Opatusos/SNES_TST/Firmware/ip/snes_tst_cpu/synthesis/submodules/snes_tst_cpu_nios2_gen2_0_cpu.v

//Legal Notice: (C)2021 Altera Corporation. All rights reserved.  Your
//use of Altera Corporation's design tools, logic functions and other
//software and tools, and its AMPP partner logic functions, and any
//output files any of the foregoing (including device programming or
//simulation files), and any associated documentation or information are
//expressly subject to the terms and conditions of the Altera Program
//License Subscription Agreement or other applicable license agreement,
//including, without limitation, that your use is for the sole purpose
//of programming logic devices manufactured by Altera and sold by Altera
//or its authorized distributors.  Please refer to the applicable
//agreement for further details.

// synthesis translate_off
`timescale 1ns / 1ps
// synthesis translate_on

// turn off superfluous verilog processor warnings 
// altera message_level Level1 
// altera message_off 10034 10035 10036 10037 10230 10240 10030 

module snes_tst_cpu_nios2_gen2_0_cpu_register_bank_a_module (
                                                              // inputs:
                                                               clock,
                                                               data,
                                                               rdaddress,
                                                               wraddress,
                                                               wren,

                                                              // outputs:
                                                               q
                                                            )
;

  parameter lpm_file = "UNUSED";


  output  [ 31: 0] q;
  input            clock;
  input   [ 31: 0] data;
  input   [  4: 0] rdaddress;
  input   [  4: 0] wraddress;
  input            wren;


wire    [ 31: 0] q;
wire    [ 31: 0] ram_data;
wire    [ 31: 0] ram_q;
  assign q = ram_q;
  assign ram_data = data;
  altsyncram the_altsyncram
    (
      .address_a (wraddress),
      .address_b (rdaddress),
      .clock0 (clock),
      .data_a (ram_data),
      .q_b (ram_q),
      .wren_a (wren)
    );

  defparam the_altsyncram.address_reg_b = "CLOCK0",
           the_altsyncram.init_file = lpm_file,
           the_altsyncram.maximum_depth = 0,
           the_altsyncram.numwords_a = 32,
           the_altsyncram.numwords_b = 32,
           the_altsyncram.operation_mode = "DUAL_PORT",
           the_altsyncram.outdata_reg_b = "UNREGISTERED",
           the_altsyncram.ram_block_type = "AUTO",
           the_altsyncram.rdcontrol_reg_b = "CLOCK0",
           the_altsyncram.read_during_write_mode_mixed_ports = "DONT_CARE",
           the_altsyncram.width_a = 32,
           the_altsyncram.width_b = 32,
           the_altsyncram.widthad_a = 5,
           the_altsyncram.widthad_b = 5;


endmodule


// synthesis translate_off
`timescale 1ns / 1ps
// synthesis translate_on

// turn off superfluous verilog processor warnings 
// altera message_level Level1 
// altera message_off 10034 10035 10036 10037 10230 10240 10030 

module snes_tst_cpu_nios2_gen2_0_cpu_register_bank_b_module (
                                                              // inputs:
                                                               clock,
                                                               data,
                                                               rdaddress,
                                                               wraddress,
                                                               wren,

                                                              // outputs:
                                                               q
                                                            )
;

  parameter lpm_file = "UNUSED";


  output  [ 31: 0] q;
  input            clock;
  input   [ 31: 0] data;
  input   [  4: 0] rdaddress;
  input   [  4: 0] wraddress;
  input            wren;


wire    [ 31: 0] q;
wire    [ 31: 0] ram_data;
wire    [ 31: 0] ram_q;
  assign q = ram_q;
  assign ram_data = data;
  altsyncram the_altsyncram
    (
      .address_a (wraddress),
      .address_b (rdaddress),
      .clock0 (clock),
      .data_a (ram_data),
      .q_b (ram_q),
      .wren_a (wren)
    );

  defparam the_altsyncram.address_reg_b = "CLOCK0",
           the_altsyncram.init_file = lpm_file,
           the_altsyncram.maximum_depth = 0,
           the_altsyncram.numwords_a = 32,
           the_altsyncram.numwords_b = 32,
           the_altsyncram.operation_mode = "DUAL_PORT",
           the_altsyncram.outdata_reg_b = "UNREGISTERED",
           the_altsyncram.ram_block_type = "AUTO",
           the_altsyncram.rdcontrol_reg_b = "CLOCK0",
           the_altsyncram.read_during_write_mode_mixed_ports = "DONT_CARE",
           the_altsyncram.width_a = 32,
           the_altsyncram.width_b = 32,
           the_altsyncram.widthad_a = 5,
           the_altsyncram.widthad_b = 5;


endmodule


// synthesis translate_off
`timescale 1ns / 1ps
// synthesis translate_on

// turn off superfluous verilog processor warnings 
// altera message_level Level1 
// altera message_off 10034 10035 10036 10037 10230 10240 10030 

module snes_tst_cpu_nios2_gen2_0_cpu_nios2_oci_debug (
                                                       // inputs:
                                                        clk,
                                                        dbrk_break,
                                                        debugreq,
                                                        hbreak_enabled,
                                                        jdo,
                                                        jrst_n,
                                                        ocireg_ers,
                                                        ocireg_mrs,
                                                        reset,
                                                        st_ready_test_idle,
                                                        take_action_ocimem_a,
                                                        take_action_ocireg,
                                                        xbrk_break,

                                                       // outputs:
                                                        debugack,
                                                        monitor_error,
                                                        monitor_go,
                                                        monitor_ready,
                                                        oci_hbreak_req,
                                                        resetlatch,
                                                        resetrequest
                                                     )
;

  output           debugack;
  output           monitor_error;
  output           monitor_go;
  output           monitor_ready;
  output           oci_hbreak_req;
  output           resetlatch;
  output           resetrequest;
  input            clk;
  input            dbrk_break;
  input            debugreq;
  input            hbreak_enabled;
  input   [ 37: 0] jdo;
  input            jrst_n;
  input            ocireg_ers;
  input            ocireg_mrs;
  input            reset;
  input            st_ready_test_idle;
  input            take_action_ocimem_a;
  input            take_action_ocireg;
  input            xbrk_break;


reg              break_on_reset /* synthesis ALTERA_ATTRIBUTE = "SUPPRESS_DA_RULE_INTERNAL=\"D101,R101\""  */;
wire             debugack;
reg              jtag_break /* synthesis ALTERA_ATTRIBUTE = "SUPPRESS_DA_RULE_INTERNAL=\"D101,R101\""  */;
reg              monitor_error /* synthesis ALTERA_ATTRIBUTE = "SUPPRESS_DA_RULE_INTERNAL=D101"  */;
reg              monitor_go /* synthesis ALTERA_ATTRIBUTE = "SUPPRESS_DA_RULE_INTERNAL=D101"  */;
reg              monitor_ready /* synthesis ALTERA_ATTRIBUTE = "SUPPRESS_DA_RULE_INTERNAL=D101"  */;
wire             oci_hbreak_req;
wire             reset_sync;
reg              resetlatch /* synthesis ALTERA_ATTRIBUTE = "SUPPRESS_DA_RULE_INTERNAL=\"D101,R101\""  */;
reg              resetrequest /* synthesis ALTERA_ATTRIBUTE = "SUPPRESS_DA_RULE_INTERNAL=\"D101,R101\""  */;
wire             unxcomplemented_resetxx0;
  assign unxcomplemented_resetxx0 = jrst_n;
  altera_std_synchronizer the_altera_std_synchronizer
    (
      .clk (clk),
      .din (reset),
      .dout (reset_sync),
      .reset_n (unxcomplemented_resetxx0)
    );

  defparam the_altera_std_synchronizer.depth = 2;

  always @(posedge clk or negedge jrst_n)
    begin
      if (jrst_n == 0)
        begin
          resetrequest <= 1'b0;
          break_on_reset <= 1'b0;
          jtag_break <= 1'b0;
        end
      else if (take_action_ocimem_a)
        begin
          resetrequest <= jdo[22];
          jtag_break <= jdo[21]     ? 1 
                    : jdo[20]  ? 0 
                    : jtag_break;

          break_on_reset <= jdo[19]     ? 1
                    : jdo[18]  ? 0
                    :  break_on_reset;

          resetlatch <= jdo[24] ? 0 : resetlatch;
        end
      else if (reset_sync)
        begin
          jtag_break <= break_on_reset;
          resetlatch <= 1;
        end
      else if (debugreq & ~debugack & break_on_reset)
          jtag_break <= 1'b1;
    end


  always @(posedge clk or negedge jrst_n)
    begin
      if (jrst_n == 0)
        begin
          monitor_ready <= 1'b0;
          monitor_error <= 1'b0;
          monitor_go <= 1'b0;
        end
      else 
        begin
          if (take_action_ocimem_a && jdo[25])
              monitor_ready <= 1'b0;
          else if (take_action_ocireg && ocireg_mrs)
              monitor_ready <= 1'b1;
          if (take_action_ocimem_a && jdo[25])
              monitor_error <= 1'b0;
          else if (take_action_ocireg && ocireg_ers)
              monitor_error <= 1'b1;
          if (take_action_ocimem_a && jdo[23])
              monitor_go <= 1'b1;
          else if (st_ready_test_idle)
              monitor_go <= 1'b0;
        end
    end


  assign oci_hbreak_req = jtag_break | dbrk_break | xbrk_break | debugreq;
  assign debugack = ~hbreak_enabled;

endmodule


// synthesis translate_off
`timescale 1ns / 1ps
// synthesis translate_on

// turn off superfluous verilog processor warnings 
// altera message_level Level1 
// altera message_off 10034 10035 10036 10037 10230 10240 10030 

module snes_tst_cpu_nios2_gen2_0_cpu_nios2_oci_break (
                                                       // inputs:
                                                        clk,
                                                        dbrk_break,
                                                        dbrk_goto0,
                                                        dbrk_goto1,
                                                        jdo,
                                                        jrst_n,
                                                        take_action_break_a,
                                                        take_action_break_b,
                                                        take_action_break_c,
                                                        take_no_action_break_a,
                                                        take_no_action_break_b,
                                                        take_no_action_break_c,
                                                        xbrk_goto0,
                                                        xbrk_goto1,

                                                       // outputs:
                                                        break_readreg,
                                                        dbrk_hit0_latch,
                                                        dbrk_hit1_latch,
                                                        dbrk_hit2_latch,
                                                        dbrk_hit3_latch,
                                                        trigbrktype,
                                                        trigger_state_0,
                                                        trigger_state_1,
                                                        xbrk_ctrl0,
                                                        xbrk_ctrl1,
                                                        xbrk_ctrl2,
                                                        xbrk_ctrl3
                                                     )
;

  output  [ 31: 0] break_readreg;
  output           dbrk_hit0_latch;
  output           dbrk_hit1_latch;
  output           dbrk_hit2_latch;
  output           dbrk_hit3_latch;
  output           trigbrktype;
  output           trigger_state_0;
  output           trigger_state_1;
  output  [  7: 0] xbrk_ctrl0;
  output  [  7: 0] xbrk_ctrl1;
  output  [  7: 0] xbrk_ctrl2;
  output  [  7: 0] xbrk_ctrl3;
  input            clk;
  input            dbrk_break;
  input            dbrk_goto0;
  input            dbrk_goto1;
  input   [ 37: 0] jdo;
  input            jrst_n;
  input            take_action_break_a;
  input            take_action_break_b;
  input            take_action_break_c;
  input            take_no_action_break_a;
  input            take_no_action_break_b;
  input            take_no_action_break_c;
  input            xbrk_goto0;
  input            xbrk_goto1;


wire    [  3: 0] break_a_wpr;
wire    [  1: 0] break_a_wpr_high_bits;
wire    [  1: 0] break_a_wpr_low_bits;
wire    [  1: 0] break_b_rr;
wire    [  1: 0] break_c_rr;
reg     [ 31: 0] break_readreg /* synthesis ALTERA_ATTRIBUTE = "SUPPRESS_DA_RULE_INTERNAL=\"D101,R101\""  */;
wire             dbrk0_high_value;
wire             dbrk0_low_value;
wire             dbrk1_high_value;
wire             dbrk1_low_value;
wire             dbrk2_high_value;
wire             dbrk2_low_value;
wire             dbrk3_high_value;
wire             dbrk3_low_value;
wire             dbrk_hit0_latch;
wire             dbrk_hit1_latch;
wire             dbrk_hit2_latch;
wire             dbrk_hit3_latch;
wire             take_action_any_break;
reg              trigbrktype /* synthesis ALTERA_ATTRIBUTE = "SUPPRESS_DA_RULE_INTERNAL=\"D101,R101\""  */;
reg              trigger_state;
wire             trigger_state_0;
wire             trigger_state_1;
wire    [ 31: 0] xbrk0_value;
wire    [ 31: 0] xbrk1_value;
wire    [ 31: 0] xbrk2_value;
wire    [ 31: 0] xbrk3_value;
reg     [  7: 0] xbrk_ctrl0 /* synthesis ALTERA_ATTRIBUTE = "SUPPRESS_DA_RULE_INTERNAL=\"D101,R101\""  */;
reg     [  7: 0] xbrk_ctrl1 /* synthesis ALTERA_ATTRIBUTE = "SUPPRESS_DA_RULE_INTERNAL=\"D101,R101\""  */;
reg     [  7: 0] xbrk_ctrl2 /* synthesis ALTERA_ATTRIBUTE = "SUPPRESS_DA_RULE_INTERNAL=\"D101,R101\""  */;
reg     [  7: 0] xbrk_ctrl3 /* synthesis ALTERA_ATTRIBUTE = "SUPPRESS_DA_RULE_INTERNAL=\"D101,R101\""  */;
  assign break_a_wpr = jdo[35 : 32];
  assign break_a_wpr_high_bits = break_a_wpr[3 : 2];
  assign break_a_wpr_low_bits = break_a_wpr[1 : 0];
  assign break_b_rr = jdo[33 : 32];
  assign break_c_rr = jdo[33 : 32];
  assign take_action_any_break = take_action_break_a | take_action_break_b | take_action_break_c;
  always @(posedge clk or negedge jrst_n)
    begin
      if (jrst_n == 0)
        begin
          xbrk_ctrl0 <= 0;
          xbrk_ctrl1 <= 0;
          xbrk_ctrl2 <= 0;
          xbrk_ctrl3 <= 0;
          trigbrktype <= 0;
        end
      else 
        begin
          if (take_action_any_break)
              trigbrktype <= 0;
          else if (dbrk_break)
              trigbrktype <= 1;
          if (take_action_break_b)
            begin
              if ((break_b_rr == 2'b00) && (0 >= 1))
                begin
                  xbrk_ctrl0[0] <= jdo[27];
                  xbrk_ctrl0[1] <= jdo[28];
                  xbrk_ctrl0[2] <= jdo[29];
                  xbrk_ctrl0[3] <= jdo[30];
                  xbrk_ctrl0[4] <= jdo[21];
                  xbrk_ctrl0[5] <= jdo[20];
                  xbrk_ctrl0[6] <= jdo[19];
                  xbrk_ctrl0[7] <= jdo[18];
                end
              if ((break_b_rr == 2'b01) && (0 >= 2))
                begin
                  xbrk_ctrl1[0] <= jdo[27];
                  xbrk_ctrl1[1] <= jdo[28];
                  xbrk_ctrl1[2] <= jdo[29];
                  xbrk_ctrl1[3] <= jdo[30];
                  xbrk_ctrl1[4] <= jdo[21];
                  xbrk_ctrl1[5] <= jdo[20];
                  xbrk_ctrl1[6] <= jdo[19];
                  xbrk_ctrl1[7] <= jdo[18];
                end
              if ((break_b_rr == 2'b10) && (0 >= 3))
                begin
                  xbrk_ctrl2[0] <= jdo[27];
                  xbrk_ctrl2[1] <= jdo[28];
                  xbrk_ctrl2[2] <= jdo[29];
                  xbrk_ctrl2[3] <= jdo[30];
                  xbrk_ctrl2[4] <= jdo[21];
                  xbrk_ctrl2[5] <= jdo[20];
                  xbrk_ctrl2[6] <= jdo[19];
                  xbrk_ctrl2[7] <= jdo[18];
                end
              if ((break_b_rr == 2'b11) && (0 >= 4))
                begin
                  xbrk_ctrl3[0] <= jdo[27];
                  xbrk_ctrl3[1] <= jdo[28];
                  xbrk_ctrl3[2] <= jdo[29];
                  xbrk_ctrl3[3] <= jdo[30];
                  xbrk_ctrl3[4] <= jdo[21];
                  xbrk_ctrl3[5] <= jdo[20];
                  xbrk_ctrl3[6] <= jdo[19];
                  xbrk_ctrl3[7] <= jdo[18];
                end
            end
        end
    end


  assign dbrk_hit0_latch = 1'b0;
  assign dbrk0_low_value = 0;
  assign dbrk0_high_value = 0;
  assign dbrk_hit1_latch = 1'b0;
  assign dbrk1_low_value = 0;
  assign dbrk1_high_value = 0;
  assign dbrk_hit2_latch = 1'b0;
  assign dbrk2_low_value = 0;
  assign dbrk2_high_value = 0;
  assign dbrk_hit3_latch = 1'b0;
  assign dbrk3_low_value = 0;
  assign dbrk3_high_value = 0;
  assign xbrk0_value = 32'b0;
  assign xbrk1_value = 32'b0;
  assign xbrk2_value = 32'b0;
  assign xbrk3_value = 32'b0;
  always @(posedge clk or negedge jrst_n)
    begin
      if (jrst_n == 0)
          break_readreg <= 32'b0;
      else if (take_action_any_break)
          break_readreg <= jdo[31 : 0];
      else if (take_no_action_break_a)
          case (break_a_wpr_high_bits)
          
              2'd0: begin
                  case (break_a_wpr_low_bits) // synthesis full_case
                  
                      2'd0: begin
                          break_readreg <= xbrk0_value;
                      end // 2'd0 
                  
                      2'd1: begin
                          break_readreg <= xbrk1_value;
                      end // 2'd1 
                  
                      2'd2: begin
                          break_readreg <= xbrk2_value;
                      end // 2'd2 
                  
                      2'd3: begin
                          break_readreg <= xbrk3_value;
                      end // 2'd3 
                  
                  endcase // break_a_wpr_low_bits
              end // 2'd0 
          
              2'd1: begin
                  break_readreg <= 32'b0;
              end // 2'd1 
          
              2'd2: begin
                  case (break_a_wpr_low_bits) // synthesis full_case
                  
                      2'd0: begin
                          break_readreg <= dbrk0_low_value;
                      end // 2'd0 
                  
                      2'd1: begin
                          break_readreg <= dbrk1_low_value;
                      end // 2'd1 
                  
                      2'd2: begin
                          break_readreg <= dbrk2_low_value;
                      end // 2'd2 
                  
                      2'd3: begin
                          break_readreg <= dbrk3_low_value;
                      end // 2'd3 
                  
                  endcase // break_a_wpr_low_bits
              end // 2'd2 
          
              2'd3: begin
                  case (break_a_wpr_low_bits) // synthesis full_case
                  
                      2'd0: begin
                          break_readreg <= dbrk0_high_value;
                      end // 2'd0 
                  
                      2'd1: begin
                          break_readreg <= dbrk1_high_value;
                      end // 2'd1 
                  
                      2'd2: begin
                          break_readreg <= dbrk2_high_value;
                      end // 2'd2 
                  
                      2'd3: begin
                          break_readreg <= dbrk3_high_value;
                      end // 2'd3 
                  
                  endcase // break_a_wpr_low_bits
              end // 2'd3 
          
          endcase // break_a_wpr_high_bits
      else if (take_no_action_break_b)
          break_readreg <= jdo[31 : 0];
      else if (take_no_action_break_c)
          break_readreg <= jdo[31 : 0];
    end


  always @(posedge clk or negedge jrst_n)
    begin
      if (jrst_n == 0)
          trigger_state <= 0;
      else if (trigger_state_1 & (xbrk_goto0 | dbrk_goto0))
          trigger_state <= 0;
      else if (trigger_state_0 & (xbrk_goto1 | dbrk_goto1))
          trigger_state <= -1;
    end


  assign trigger_state_0 = ~trigger_state;
  assign trigger_state_1 = trigger_state;

endmodule


// synthesis translate_off
`timescale 1ns / 1ps
// synthesis translate_on

// turn off superfluous verilog processor warnings 
// altera message_level Level1 
// altera message_off 10034 10035 10036 10037 10230 10240 10030 

module snes_tst_cpu_nios2_gen2_0_cpu_nios2_oci_xbrk (
                                                      // inputs:
                                                       D_valid,
                                                       E_valid,
                                                       F_pc,
                                                       clk,
                                                       reset_n,
                                                       trigger_state_0,
                                                       trigger_state_1,
                                                       xbrk_ctrl0,
                                                       xbrk_ctrl1,
                                                       xbrk_ctrl2,
                                                       xbrk_ctrl3,

                                                      // outputs:
                                                       xbrk_break,
                                                       xbrk_goto0,
                                                       xbrk_goto1,
                                                       xbrk_traceoff,
                                                       xbrk_traceon,
                                                       xbrk_trigout
                                                    )
;

  output           xbrk_break;
  output           xbrk_goto0;
  output           xbrk_goto1;
  output           xbrk_traceoff;
  output           xbrk_traceon;
  output           xbrk_trigout;
  input            D_valid;
  input            E_valid;
  input   [ 17: 0] F_pc;
  input            clk;
  input            reset_n;
  input            trigger_state_0;
  input            trigger_state_1;
  input   [  7: 0] xbrk_ctrl0;
  input   [  7: 0] xbrk_ctrl1;
  input   [  7: 0] xbrk_ctrl2;
  input   [  7: 0] xbrk_ctrl3;


wire             D_cpu_addr_en;
wire             E_cpu_addr_en;
reg              E_xbrk_goto0;
reg              E_xbrk_goto1;
reg              E_xbrk_traceoff;
reg              E_xbrk_traceon;
reg              E_xbrk_trigout;
wire    [ 19: 0] cpu_i_address;
wire             xbrk0_armed;
wire             xbrk0_break_hit;
wire             xbrk0_goto0_hit;
wire             xbrk0_goto1_hit;
wire             xbrk0_toff_hit;
wire             xbrk0_ton_hit;
wire             xbrk0_tout_hit;
wire             xbrk1_armed;
wire             xbrk1_break_hit;
wire             xbrk1_goto0_hit;
wire             xbrk1_goto1_hit;
wire             xbrk1_toff_hit;
wire             xbrk1_ton_hit;
wire             xbrk1_tout_hit;
wire             xbrk2_armed;
wire             xbrk2_break_hit;
wire             xbrk2_goto0_hit;
wire             xbrk2_goto1_hit;
wire             xbrk2_toff_hit;
wire             xbrk2_ton_hit;
wire             xbrk2_tout_hit;
wire             xbrk3_armed;
wire             xbrk3_break_hit;
wire             xbrk3_goto0_hit;
wire             xbrk3_goto1_hit;
wire             xbrk3_toff_hit;
wire             xbrk3_ton_hit;
wire             xbrk3_tout_hit;
reg              xbrk_break;
wire             xbrk_break_hit;
wire             xbrk_goto0;
wire             xbrk_goto0_hit;
wire             xbrk_goto1;
wire             xbrk_goto1_hit;
wire             xbrk_toff_hit;
wire             xbrk_ton_hit;
wire             xbrk_tout_hit;
wire             xbrk_traceoff;
wire             xbrk_traceon;
wire             xbrk_trigout;
  assign cpu_i_address = {F_pc, 2'b00};
  assign D_cpu_addr_en = D_valid;
  assign E_cpu_addr_en = E_valid;
  assign xbrk0_break_hit = 0;
  assign xbrk0_ton_hit = 0;
  assign xbrk0_toff_hit = 0;
  assign xbrk0_tout_hit = 0;
  assign xbrk0_goto0_hit = 0;
  assign xbrk0_goto1_hit = 0;
  assign xbrk1_break_hit = 0;
  assign xbrk1_ton_hit = 0;
  assign xbrk1_toff_hit = 0;
  assign xbrk1_tout_hit = 0;
  assign xbrk1_goto0_hit = 0;
  assign xbrk1_goto1_hit = 0;
  assign xbrk2_break_hit = 0;
  assign xbrk2_ton_hit = 0;
  assign xbrk2_toff_hit = 0;
  assign xbrk2_tout_hit = 0;
  assign xbrk2_goto0_hit = 0;
  assign xbrk2_goto1_hit = 0;
  assign xbrk3_break_hit = 0;
  assign xbrk3_ton_hit = 0;
  assign xbrk3_toff_hit = 0;
  assign xbrk3_tout_hit = 0;
  assign xbrk3_goto0_hit = 0;
  assign xbrk3_goto1_hit = 0;
  assign xbrk_break_hit = (xbrk0_break_hit) | (xbrk1_break_hit) | (xbrk2_break_hit) | (xbrk3_break_hit);
  assign xbrk_ton_hit = (xbrk0_ton_hit) | (xbrk1_ton_hit) | (xbrk2_ton_hit) | (xbrk3_ton_hit);
  assign xbrk_toff_hit = (xbrk0_toff_hit) | (xbrk1_toff_hit) | (xbrk2_toff_hit) | (xbrk3_toff_hit);
  assign xbrk_tout_hit = (xbrk0_tout_hit) | (xbrk1_tout_hit) | (xbrk2_tout_hit) | (xbrk3_tout_hit);
  assign xbrk_goto0_hit = (xbrk0_goto0_hit) | (xbrk1_goto0_hit) | (xbrk2_goto0_hit) | (xbrk3_goto0_hit);
  assign xbrk_goto1_hit = (xbrk0_goto1_hit) | (xbrk1_goto1_hit) | (xbrk2_goto1_hit) | (xbrk3_goto1_hit);
  always @(posedge clk or negedge reset_n)
    begin
      if (reset_n == 0)
          xbrk_break <= 0;
      else if (E_cpu_addr_en)
          xbrk_break <= xbrk_break_hit;
    end


  always @(posedge clk or negedge reset_n)
    begin
      if (reset_n == 0)
          E_xbrk_traceon <= 0;
      else if (E_cpu_addr_en)
          E_xbrk_traceon <= xbrk_ton_hit;
    end


  always @(posedge clk or negedge reset_n)
    begin
      if (reset_n == 0)
          E_xbrk_traceoff <= 0;
      else if (E_cpu_addr_en)
          E_xbrk_traceoff <= xbrk_toff_hit;
    end


  always @(posedge clk or negedge reset_n)
    begin
      if (reset_n == 0)
          E_xbrk_trigout <= 0;
      else if (E_cpu_addr_en)
          E_xbrk_trigout <= xbrk_tout_hit;
    end


  always @(posedge clk or negedge reset_n)
    begin
      if (reset_n == 0)
          E_xbrk_goto0 <= 0;
      else if (E_cpu_addr_en)
          E_xbrk_goto0 <= xbrk_goto0_hit;
    end


  always @(posedge clk or negedge reset_n)
    begin
      if (reset_n == 0)
          E_xbrk_goto1 <= 0;
      else if (E_cpu_addr_en)
          E_xbrk_goto1 <= xbrk_goto1_hit;
    end


  assign xbrk_traceon = 1'b0;
  assign xbrk_traceoff = 1'b0;
  assign xbrk_trigout = 1'b0;
  assign xbrk_goto0 = 1'b0;
  assign xbrk_goto1 = 1'b0;
  assign xbrk0_armed = (xbrk_ctrl0[4] & trigger_state_0) ||
    (xbrk_ctrl0[5] & trigger_state_1);

  assign xbrk1_armed = (xbrk_ctrl1[4] & trigger_state_0) ||
    (xbrk_ctrl1[5] & trigger_state_1);

  assign xbrk2_armed = (xbrk_ctrl2[4] & trigger_state_0) ||
    (xbrk_ctrl2[5] & trigger_state_1);

  assign xbrk3_armed = (xbrk_ctrl3[4] & trigger_state_0) ||
    (xbrk_ctrl3[5] & trigger_state_1);


endmodule


// synthesis translate_off
`timescale 1ns / 1ps
// synthesis translate_on

// turn off superfluous verilog processor warnings 
// altera message_level Level1 
// altera message_off 10034 10035 10036 10037 10230 10240 10030 

module snes_tst_cpu_nios2_gen2_0_cpu_nios2_oci_dbrk (
                                                      // inputs:
                                                       E_st_data,
                                                       av_ld_data_aligned_filtered,
                                                       clk,
                                                       d_address,
                                                       d_read,
                                                       d_waitrequest,
                                                       d_write,
                                                       debugack,
                                                       reset_n,

                                                      // outputs:
                                                       cpu_d_address,
                                                       cpu_d_read,
                                                       cpu_d_readdata,
                                                       cpu_d_wait,
                                                       cpu_d_write,
                                                       cpu_d_writedata,
                                                       dbrk_break,
                                                       dbrk_goto0,
                                                       dbrk_goto1,
                                                       dbrk_traceme,
                                                       dbrk_traceoff,
                                                       dbrk_traceon,
                                                       dbrk_trigout
                                                    )
;

  output  [ 19: 0] cpu_d_address;
  output           cpu_d_read;
  output  [ 31: 0] cpu_d_readdata;
  output           cpu_d_wait;
  output           cpu_d_write;
  output  [ 31: 0] cpu_d_writedata;
  output           dbrk_break;
  output           dbrk_goto0;
  output           dbrk_goto1;
  output           dbrk_traceme;
  output           dbrk_traceoff;
  output           dbrk_traceon;
  output           dbrk_trigout;
  input   [ 31: 0] E_st_data;
  input   [ 31: 0] av_ld_data_aligned_filtered;
  input            clk;
  input   [ 19: 0] d_address;
  input            d_read;
  input            d_waitrequest;
  input            d_write;
  input            debugack;
  input            reset_n;


wire    [ 19: 0] cpu_d_address;
wire             cpu_d_read;
wire    [ 31: 0] cpu_d_readdata;
wire             cpu_d_wait;
wire             cpu_d_write;
wire    [ 31: 0] cpu_d_writedata;
wire             dbrk0_armed;
wire             dbrk0_break_pulse;
wire             dbrk0_goto0;
wire             dbrk0_goto1;
wire             dbrk0_traceme;
wire             dbrk0_traceoff;
wire             dbrk0_traceon;
wire             dbrk0_trigout;
wire             dbrk1_armed;
wire             dbrk1_break_pulse;
wire             dbrk1_goto0;
wire             dbrk1_goto1;
wire             dbrk1_traceme;
wire             dbrk1_traceoff;
wire             dbrk1_traceon;
wire             dbrk1_trigout;
wire             dbrk2_armed;
wire             dbrk2_break_pulse;
wire             dbrk2_goto0;
wire             dbrk2_goto1;
wire             dbrk2_traceme;
wire             dbrk2_traceoff;
wire             dbrk2_traceon;
wire             dbrk2_trigout;
wire             dbrk3_armed;
wire             dbrk3_break_pulse;
wire             dbrk3_goto0;
wire             dbrk3_goto1;
wire             dbrk3_traceme;
wire             dbrk3_traceoff;
wire             dbrk3_traceon;
wire             dbrk3_trigout;
reg              dbrk_break;
reg              dbrk_break_pulse;
wire    [ 31: 0] dbrk_data;
reg              dbrk_goto0;
reg              dbrk_goto1;
reg              dbrk_traceme;
reg              dbrk_traceoff;
reg              dbrk_traceon;
reg              dbrk_trigout;
  assign cpu_d_address = d_address;
  assign cpu_d_readdata = av_ld_data_aligned_filtered;
  assign cpu_d_read = d_read;
  assign cpu_d_writedata = E_st_data;
  assign cpu_d_write = d_write;
  assign cpu_d_wait = d_waitrequest;
  assign dbrk_data = cpu_d_write ? cpu_d_writedata : cpu_d_readdata;
  always @(posedge clk or negedge reset_n)
    begin
      if (reset_n == 0)
          dbrk_break <= 0;
      else 
        dbrk_break <= dbrk_break   ? ~debugack   
                : dbrk_break_pulse;

    end


  assign dbrk0_armed = 1'b0;
  assign dbrk0_trigout = 1'b0;
  assign dbrk0_break_pulse = 1'b0;
  assign dbrk0_traceoff = 1'b0;
  assign dbrk0_traceon = 1'b0;
  assign dbrk0_traceme = 1'b0;
  assign dbrk0_goto0 = 1'b0;
  assign dbrk0_goto1 = 1'b0;
  assign dbrk1_armed = 1'b0;
  assign dbrk1_trigout = 1'b0;
  assign dbrk1_break_pulse = 1'b0;
  assign dbrk1_traceoff = 1'b0;
  assign dbrk1_traceon = 1'b0;
  assign dbrk1_traceme = 1'b0;
  assign dbrk1_goto0 = 1'b0;
  assign dbrk1_goto1 = 1'b0;
  assign dbrk2_armed = 1'b0;
  assign dbrk2_trigout = 1'b0;
  assign dbrk2_break_pulse = 1'b0;
  assign dbrk2_traceoff = 1'b0;
  assign dbrk2_traceon = 1'b0;
  assign dbrk2_traceme = 1'b0;
  assign dbrk2_goto0 = 1'b0;
  assign dbrk2_goto1 = 1'b0;
  assign dbrk3_armed = 1'b0;
  assign dbrk3_trigout = 1'b0;
  assign dbrk3_break_pulse = 1'b0;
  assign dbrk3_traceoff = 1'b0;
  assign dbrk3_traceon = 1'b0;
  assign dbrk3_traceme = 1'b0;
  assign dbrk3_goto0 = 1'b0;
  assign dbrk3_goto1 = 1'b0;
  always @(posedge clk or negedge reset_n)
    begin
      if (reset_n == 0)
        begin
          dbrk_trigout <= 0;
          dbrk_break_pulse <= 0;
          dbrk_traceoff <= 0;
          dbrk_traceon <= 0;
          dbrk_traceme <= 0;
          dbrk_goto0 <= 0;
          dbrk_goto1 <= 0;
        end
      else 
        begin
          dbrk_trigout <= dbrk0_trigout | dbrk1_trigout | dbrk2_trigout | dbrk3_trigout;
          dbrk_break_pulse <= dbrk0_break_pulse | dbrk1_break_pulse | dbrk2_break_pulse | dbrk3_break_pulse;
          dbrk_traceoff <= dbrk0_traceoff | dbrk1_traceoff | dbrk2_traceoff | dbrk3_traceoff;
          dbrk_traceon <= dbrk0_traceon | dbrk1_traceon | dbrk2_traceon | dbrk3_traceon;
          dbrk_traceme <= dbrk0_traceme | dbrk1_traceme | dbrk2_traceme | dbrk3_traceme;
          dbrk_goto0 <= dbrk0_goto0 | dbrk1_goto0 | dbrk2_goto0 | dbrk3_goto0;
          dbrk_goto1 <= dbrk0_goto1 | dbrk1_goto1 | dbrk2_goto1 | dbrk3_goto1;
        end
    end



endmodule


// synthesis translate_off
`timescale 1ns / 1ps
// synthesis translate_on

// turn off superfluous verilog processor warnings 
// altera message_level Level1 
// altera message_off 10034 10035 10036 10037 10230 10240 10030 

module snes_tst_cpu_nios2_gen2_0_cpu_nios2_oci_itrace (
                                                        // inputs:
                                                         clk,
                                                         dbrk_traceoff,
                                                         dbrk_traceon,
                                                         jdo,
                                                         jrst_n,
                                                         take_action_tracectrl,
                                                         xbrk_traceoff,
                                                         xbrk_traceon,
                                                         xbrk_wrap_traceoff,

                                                        // outputs:
                                                         itm,
                                                         trc_ctrl,
                                                         trc_on
                                                      )
;

  output  [ 35: 0] itm;
  output  [ 15: 0] trc_ctrl;
  output           trc_on;
  input            clk;
  input            dbrk_traceoff;
  input            dbrk_traceon;
  input   [ 15: 0] jdo;
  input            jrst_n;
  input            take_action_tracectrl;
  input            xbrk_traceoff;
  input            xbrk_traceon;
  input            xbrk_wrap_traceoff;


wire             advanced_exc_occured;
wire             curr_pid;
wire    [  1: 0] dct_code;
wire             dct_is_taken;
wire    [ 31: 0] eic_addr;
wire    [ 31: 0] exc_addr;
wire             instr_retired;
wire             is_cond_dct;
wire             is_dct;
wire             is_exception_no_break;
wire             is_external_interrupt;
wire             is_fast_tlb_miss_exception;
wire             is_idct;
wire    [ 35: 0] itm;
wire             not_in_debug_mode;
wire             record_dct_outcome_in_sync;
wire             record_itrace;
wire    [ 31: 0] retired_pcb;
wire    [  1: 0] sync_code;
wire    [  6: 0] sync_interval;
wire    [  6: 0] sync_timer;
wire    [  6: 0] sync_timer_next;
wire             sync_timer_reached_zero;
wire    [ 15: 0] trc_ctrl;
reg     [ 10: 0] trc_ctrl_reg /* synthesis ALTERA_ATTRIBUTE = "SUPPRESS_DA_RULE_INTERNAL=\"D101,D103,R101\""  */;
wire             trc_on;
  assign is_cond_dct = 1'b0;
  assign is_dct = 1'b0;
  assign dct_is_taken = 1'b0;
  assign is_idct = 1'b0;
  assign retired_pcb = 32'b0;
  assign not_in_debug_mode = 1'b0;
  assign instr_retired = 1'b0;
  assign advanced_exc_occured = 1'b0;
  assign is_exception_no_break = 1'b0;
  assign is_external_interrupt = 1'b0;
  assign is_fast_tlb_miss_exception = 1'b0;
  assign curr_pid = 1'b0;
  assign exc_addr = 32'b0;
  assign eic_addr = 32'b0;
  assign sync_code = trc_ctrl[3 : 2];
  assign sync_interval = { sync_code[1] & sync_code[0], 1'b0, sync_code[1] & ~sync_code[0], 1'b0, ~sync_code[1] & sync_code[0], 2'b00 };
  assign sync_timer_reached_zero = sync_timer == 0;
  assign record_dct_outcome_in_sync = dct_is_taken & sync_timer_reached_zero;
  assign sync_timer_next = sync_timer_reached_zero ? sync_timer : (sync_timer - 1);
  assign record_itrace = trc_on & trc_ctrl[4];
  assign dct_code = {is_cond_dct, dct_is_taken};
  assign itm = 36'd0;
  assign sync_timer = 7'd1;
  always @(posedge clk or negedge jrst_n)
    begin
      if (jrst_n == 0)
        begin
          trc_ctrl_reg[0] <= 1'b0;
          trc_ctrl_reg[1] <= 1'b0;
          trc_ctrl_reg[3 : 2] <= 2'b00;
          trc_ctrl_reg[4] <= 1'b0;
          trc_ctrl_reg[7 : 5] <= 3'b000;
          trc_ctrl_reg[8] <= 0;
          trc_ctrl_reg[9] <= 1'b0;
          trc_ctrl_reg[10] <= 1'b0;
        end
      else if (take_action_tracectrl)
        begin
          trc_ctrl_reg[0] <= jdo[5];
          trc_ctrl_reg[1] <= jdo[6];
          trc_ctrl_reg[3 : 2] <= jdo[8 : 7];
          trc_ctrl_reg[4] <= jdo[9];
          trc_ctrl_reg[9] <= jdo[14];
          trc_ctrl_reg[10] <= jdo[2];
          trc_ctrl_reg[7 : 5] <= 3'b000;
          trc_ctrl_reg[8] <= 1'b0;
        end
      else if (xbrk_wrap_traceoff)
        begin
          trc_ctrl_reg[1] <= 0;
          trc_ctrl_reg[0] <= 0;
        end
      else if (dbrk_traceoff | xbrk_traceoff)
          trc_ctrl_reg[1] <= 0;
      else if (trc_ctrl_reg[0] & 
                                  (dbrk_traceon | xbrk_traceon))
          trc_ctrl_reg[1] <= 1;
    end


  assign trc_ctrl = 0;
  assign trc_on = trc_ctrl[1] & (trc_ctrl[9] | not_in_debug_mode);

endmodule


// synthesis translate_off
`timescale 1ns / 1ps
// synthesis translate_on

// turn off superfluous verilog processor warnings 
// altera message_level Level1 
// altera message_off 10034 10035 10036 10037 10230 10240 10030 

module snes_tst_cpu_nios2_gen2_0_cpu_nios2_oci_td_mode (
                                                         // inputs:
                                                          ctrl,

                                                         // outputs:
                                                          td_mode
                                                       )
;

  output  [  3: 0] td_mode;
  input   [  8: 0] ctrl;


wire    [  2: 0] ctrl_bits_for_mux;
reg     [  3: 0] td_mode;
  assign ctrl_bits_for_mux = ctrl[7 : 5];
  always @(ctrl_bits_for_mux)
    begin
      case (ctrl_bits_for_mux)
      
          3'b000: begin
              td_mode = 4'b0000;
          end // 3'b000 
      
          3'b001: begin
              td_mode = 4'b1000;
          end // 3'b001 
      
          3'b010: begin
              td_mode = 4'b0100;
          end // 3'b010 
      
          3'b011: begin
              td_mode = 4'b1100;
          end // 3'b011 
      
          3'b100: begin
              td_mode = 4'b0010;
          end // 3'b100 
      
          3'b101: begin
              td_mode = 4'b1010;
          end // 3'b101 
      
          3'b110: begin
              td_mode = 4'b0101;
          end // 3'b110 
      
          3'b111: begin
              td_mode = 4'b1111;
          end // 3'b111 
      
      endcase // ctrl_bits_for_mux
    end



endmodule


// synthesis translate_off
`timescale 1ns / 1ps
// synthesis translate_on

// turn off superfluous verilog processor warnings 
// altera message_level Level1 
// altera message_off 10034 10035 10036 10037 10230 10240 10030 

module snes_tst_cpu_nios2_gen2_0_cpu_nios2_oci_dtrace (
                                                        // inputs:
                                                         clk,
                                                         cpu_d_address,
                                                         cpu_d_read,
                                                         cpu_d_readdata,
                                                         cpu_d_wait,
                                                         cpu_d_write,
                                                         cpu_d_writedata,
                                                         jrst_n,
                                                         trc_ctrl,

                                                        // outputs:
                                                         atm,
                                                         dtm
                                                      )
;

  output  [ 35: 0] atm;
  output  [ 35: 0] dtm;
  input            clk;
  input   [ 19: 0] cpu_d_address;
  input            cpu_d_read;
  input   [ 31: 0] cpu_d_readdata;
  input            cpu_d_wait;
  input            cpu_d_write;
  input   [ 31: 0] cpu_d_writedata;
  input            jrst_n;
  input   [ 15: 0] trc_ctrl;


reg     [ 35: 0] atm /* synthesis ALTERA_ATTRIBUTE = "SUPPRESS_DA_RULE_INTERNAL=R101"  */;
wire    [ 31: 0] cpu_d_address_0_padded;
wire    [ 31: 0] cpu_d_readdata_0_padded;
wire    [ 31: 0] cpu_d_writedata_0_padded;
reg     [ 35: 0] dtm /* synthesis ALTERA_ATTRIBUTE = "SUPPRESS_DA_RULE_INTERNAL=R101"  */;
wire             dummy_tie_off;
wire             record_load_addr;
wire             record_load_data;
wire             record_store_addr;
wire             record_store_data;
wire    [  3: 0] td_mode_trc_ctrl;
  assign cpu_d_writedata_0_padded = cpu_d_writedata | 32'b0;
  assign cpu_d_readdata_0_padded = cpu_d_readdata | 32'b0;
  assign cpu_d_address_0_padded = cpu_d_address | 32'b0;
  //snes_tst_cpu_nios2_gen2_0_cpu_nios2_oci_trc_ctrl_td_mode, which is an e_instance
  snes_tst_cpu_nios2_gen2_0_cpu_nios2_oci_td_mode snes_tst_cpu_nios2_gen2_0_cpu_nios2_oci_trc_ctrl_td_mode
    (
      .ctrl    (trc_ctrl[8 : 0]),
      .td_mode (td_mode_trc_ctrl)
    );

  assign {record_load_addr, record_store_addr,
         record_load_data, record_store_data} = td_mode_trc_ctrl;
  always @(posedge clk or negedge jrst_n)
    begin
      if (jrst_n == 0)
        begin
          atm <= 0;
          dtm <= 0;
        end
      else 
        begin
          atm <= 0;
          dtm <= 0;
        end
    end


  assign dummy_tie_off = cpu_d_wait|cpu_d_read|cpu_d_write;

endmodule


// synthesis translate_off
`timescale 1ns / 1ps
// synthesis translate_on

// turn off superfluous verilog processor warnings 
// altera message_level Level1 
// altera message_off 10034 10035 10036 10037 10230 10240 10030 

module snes_tst_cpu_nios2_gen2_0_cpu_nios2_oci_compute_input_tm_cnt (
                                                                      // inputs:
                                                                       atm_valid,
                                                                       dtm_valid,
                                                                       itm_valid,

                                                                      // outputs:
                                                                       compute_input_tm_cnt
                                                                    )
;

  output  [  1: 0] compute_input_tm_cnt;
  input            atm_valid;
  input            dtm_valid;
  input            itm_valid;


reg     [  1: 0] compute_input_tm_cnt;
wire    [  2: 0] switch_for_mux;
  assign switch_for_mux = {itm_valid, atm_valid, dtm_valid};
  always @(switch_for_mux)
    begin
      case (switch_for_mux)
      
          3'b000: begin
              compute_input_tm_cnt = 0;
          end // 3'b000 
      
          3'b001: begin
              compute_input_tm_cnt = 1;
          end // 3'b001 
      
          3'b010: begin
              compute_input_tm_cnt = 1;
          end // 3'b010 
      
          3'b011: begin
              compute_input_tm_cnt = 2;
          end // 3'b011 
      
          3'b100: begin
              compute_input_tm_cnt = 1;
          end // 3'b100 
      
          3'b101: begin
              compute_input_tm_cnt = 2;
          end // 3'b101 
      
          3'b110: begin
              compute_input_tm_cnt = 2;
          end // 3'b110 
      
          3'b111: begin
              compute_input_tm_cnt = 3;
          end // 3'b111 
      
      endcase // switch_for_mux
    end



endmodule


// synthesis translate_off
`timescale 1ns / 1ps
// synthesis translate_on

// turn off superfluous verilog processor warnings 
// altera message_level Level1 
// altera message_off 10034 10035 10036 10037 10230 10240 10030 

module snes_tst_cpu_nios2_gen2_0_cpu_nios2_oci_fifo_wrptr_inc (
                                                                // inputs:
                                                                 ge2_free,
                                                                 ge3_free,
                                                                 input_tm_cnt,

                                                                // outputs:
                                                                 fifo_wrptr_inc
                                                              )
;

  output  [  3: 0] fifo_wrptr_inc;
  input            ge2_free;
  input            ge3_free;
  input   [  1: 0] input_tm_cnt;


reg     [  3: 0] fifo_wrptr_inc;
  always @(ge2_free or ge3_free or input_tm_cnt)
    begin
      if (ge3_free & (input_tm_cnt == 3))
          fifo_wrptr_inc = 3;
      else if (ge2_free & (input_tm_cnt >= 2))
          fifo_wrptr_inc = 2;
      else if (input_tm_cnt >= 1)
          fifo_wrptr_inc = 1;
      else 
        fifo_wrptr_inc = 0;
    end



endmodule


// synthesis translate_off
`timescale 1ns / 1ps
// synthesis translate_on

// turn off superfluous verilog processor warnings 
// altera message_level Level1 
// altera message_off 10034 10035 10036 10037 10230 10240 10030 

module snes_tst_cpu_nios2_gen2_0_cpu_nios2_oci_fifo_cnt_inc (
                                                              // inputs:
                                                               empty,
                                                               ge2_free,
                                                               ge3_free,
                                                               input_tm_cnt,

                                                              // outputs:
                                                               fifo_cnt_inc
                                                            )
;

  output  [  4: 0] fifo_cnt_inc;
  input            empty;
  input            ge2_free;
  input            ge3_free;
  input   [  1: 0] input_tm_cnt;


reg     [  4: 0] fifo_cnt_inc;
  always @(empty or ge2_free or ge3_free or input_tm_cnt)
    begin
      if (empty)
          fifo_cnt_inc = input_tm_cnt[1 : 0];
      else if (ge3_free & (input_tm_cnt == 3))
          fifo_cnt_inc = 2;
      else if (ge2_free & (input_tm_cnt >= 2))
          fifo_cnt_inc = 1;
      else if (input_tm_cnt >= 1)
          fifo_cnt_inc = 0;
      else 
        fifo_cnt_inc = {5{1'b1}};
    end



endmodule


// synthesis translate_off
`timescale 1ns / 1ps
// synthesis translate_on

// turn off superfluous verilog processor warnings 
// altera message_level Level1 
// altera message_off 10034 10035 10036 10037 10230 10240 10030 

module snes_tst_cpu_nios2_gen2_0_cpu_nios2_oci_fifo (
                                                      // inputs:
                                                       atm,
                                                       clk,
                                                       dbrk_traceme,
                                                       dbrk_traceoff,
                                                       dbrk_traceon,
                                                       dtm,
                                                       itm,
                                                       jrst_n,
                                                       reset_n,
                                                       trc_on,

                                                      // outputs:
                                                       tw
                                                    )
;

  output  [ 35: 0] tw;
  input   [ 35: 0] atm;
  input            clk;
  input            dbrk_traceme;
  input            dbrk_traceoff;
  input            dbrk_traceon;
  input   [ 35: 0] dtm;
  input   [ 35: 0] itm;
  input            jrst_n;
  input            reset_n;
  input            trc_on;


wire             atm_valid;
wire    [  1: 0] compute_input_tm_cnt;
wire             dtm_valid;
wire             empty;
reg     [ 35: 0] fifo_0;
wire             fifo_0_enable;
wire    [ 35: 0] fifo_0_mux;
reg     [ 35: 0] fifo_1;
reg     [ 35: 0] fifo_10;
wire             fifo_10_enable;
wire    [ 35: 0] fifo_10_mux;
reg     [ 35: 0] fifo_11;
wire             fifo_11_enable;
wire    [ 35: 0] fifo_11_mux;
reg     [ 35: 0] fifo_12;
wire             fifo_12_enable;
wire    [ 35: 0] fifo_12_mux;
reg     [ 35: 0] fifo_13;
wire             fifo_13_enable;
wire    [ 35: 0] fifo_13_mux;
reg     [ 35: 0] fifo_14;
wire             fifo_14_enable;
wire    [ 35: 0] fifo_14_mux;
reg     [ 35: 0] fifo_15;
wire             fifo_15_enable;
wire    [ 35: 0] fifo_15_mux;
wire             fifo_1_enable;
wire    [ 35: 0] fifo_1_mux;
reg     [ 35: 0] fifo_2;
wire             fifo_2_enable;
wire    [ 35: 0] fifo_2_mux;
reg     [ 35: 0] fifo_3;
wire             fifo_3_enable;
wire    [ 35: 0] fifo_3_mux;
reg     [ 35: 0] fifo_4;
wire             fifo_4_enable;
wire    [ 35: 0] fifo_4_mux;
reg     [ 35: 0] fifo_5;
wire             fifo_5_enable;
wire    [ 35: 0] fifo_5_mux;
reg     [ 35: 0] fifo_6;
wire             fifo_6_enable;
wire    [ 35: 0] fifo_6_mux;
reg     [ 35: 0] fifo_7;
wire             fifo_7_enable;
wire    [ 35: 0] fifo_7_mux;
reg     [ 35: 0] fifo_8;
wire             fifo_8_enable;
wire    [ 35: 0] fifo_8_mux;
reg     [ 35: 0] fifo_9;
wire             fifo_9_enable;
wire    [ 35: 0] fifo_9_mux;
reg     [  4: 0] fifo_cnt /* synthesis ALTERA_ATTRIBUTE = "SUPPRESS_DA_RULE_INTERNAL=R101"  */;
wire    [  4: 0] fifo_cnt_inc;
wire    [ 35: 0] fifo_head;
reg     [  3: 0] fifo_rdptr /* synthesis ALTERA_ATTRIBUTE = "SUPPRESS_DA_RULE_INTERNAL=R101"  */;
wire    [ 35: 0] fifo_read_mux;
reg     [  3: 0] fifo_wrptr /* synthesis ALTERA_ATTRIBUTE = "SUPPRESS_DA_RULE_INTERNAL=R101"  */;
wire    [  3: 0] fifo_wrptr_inc;
wire    [  3: 0] fifo_wrptr_plus1;
wire    [  3: 0] fifo_wrptr_plus2;
wire             ge2_free;
wire             ge3_free;
wire             input_ge1;
wire             input_ge2;
wire             input_ge3;
wire    [  1: 0] input_tm_cnt;
wire             itm_valid;
reg              overflow_pending /* synthesis ALTERA_ATTRIBUTE = "SUPPRESS_DA_RULE_INTERNAL=R101"  */;
wire    [ 35: 0] overflow_pending_atm;
wire    [ 35: 0] overflow_pending_dtm;
wire             trc_this;
wire    [ 35: 0] tw;
  assign trc_this = trc_on | (dbrk_traceon & ~dbrk_traceoff) | dbrk_traceme;
  assign itm_valid = |itm[35 : 32];
  assign atm_valid = |atm[35 : 32] & trc_this;
  assign dtm_valid = |dtm[35 : 32] & trc_this;
  assign ge2_free = ~fifo_cnt[4];
  assign ge3_free = ge2_free & ~&fifo_cnt[3 : 0];
  assign empty = ~|fifo_cnt;
  assign fifo_wrptr_plus1 = fifo_wrptr + 1;
  assign fifo_wrptr_plus2 = fifo_wrptr + 2;
  snes_tst_cpu_nios2_gen2_0_cpu_nios2_oci_compute_input_tm_cnt the_snes_tst_cpu_nios2_gen2_0_cpu_nios2_oci_compute_input_tm_cnt
    (
      .atm_valid            (atm_valid),
      .compute_input_tm_cnt (compute_input_tm_cnt),
      .dtm_valid            (dtm_valid),
      .itm_valid            (itm_valid)
    );

  assign input_tm_cnt = compute_input_tm_cnt;
  snes_tst_cpu_nios2_gen2_0_cpu_nios2_oci_fifo_wrptr_inc the_snes_tst_cpu_nios2_gen2_0_cpu_nios2_oci_fifo_wrptr_inc
    (
      .fifo_wrptr_inc (fifo_wrptr_inc),
      .ge2_free       (ge2_free),
      .ge3_free       (ge3_free),
      .input_tm_cnt   (input_tm_cnt)
    );

  snes_tst_cpu_nios2_gen2_0_cpu_nios2_oci_fifo_cnt_inc the_snes_tst_cpu_nios2_gen2_0_cpu_nios2_oci_fifo_cnt_inc
    (
      .empty        (empty),
      .fifo_cnt_inc (fifo_cnt_inc),
      .ge2_free     (ge2_free),
      .ge3_free     (ge3_free),
      .input_tm_cnt (input_tm_cnt)
    );

  always @(posedge clk or negedge jrst_n)
    begin
      if (jrst_n == 0)
        begin
          fifo_rdptr <= 0;
          fifo_wrptr <= 0;
          fifo_cnt <= 0;
          overflow_pending <= 1;
        end
      else 
        begin
          fifo_wrptr <= fifo_wrptr + fifo_wrptr_inc;
          fifo_cnt <= fifo_cnt + fifo_cnt_inc;
          if (~empty)
              fifo_rdptr <= fifo_rdptr + 1;
          if (~trc_this || (~ge2_free & input_ge2) || (~ge3_free & input_ge3))
              overflow_pending <= 1;
          else if (atm_valid | dtm_valid)
              overflow_pending <= 0;
        end
    end


  assign fifo_head = fifo_read_mux;
  assign tw = itm;
  assign fifo_0_enable = ((fifo_wrptr == 4'd0) && input_ge1)  || (ge2_free && (fifo_wrptr_plus1== 4'd0) && input_ge2)  ||(ge3_free && (fifo_wrptr_plus2== 4'd0) && input_ge3);
  always @(posedge clk or negedge reset_n)
    begin
      if (reset_n == 0)
          fifo_0 <= 0;
      else if (fifo_0_enable)
          fifo_0 <= fifo_0_mux;
    end


  assign fifo_0_mux = (((fifo_wrptr == 4'd0) && itm_valid))? itm :
    (((fifo_wrptr == 4'd0) && atm_valid))? overflow_pending_atm :
    (((fifo_wrptr == 4'd0) && dtm_valid))? overflow_pending_dtm :
    (((fifo_wrptr_plus1 == 4'd0) && (ge2_free & itm_valid & atm_valid)))? overflow_pending_atm :
    (((fifo_wrptr_plus1 == 4'd0) && (ge2_free & itm_valid & dtm_valid)))? overflow_pending_dtm :
    (((fifo_wrptr_plus1 == 4'd0) && (ge2_free & atm_valid & dtm_valid)))? overflow_pending_dtm :
    overflow_pending_dtm;

  assign fifo_1_enable = ((fifo_wrptr == 4'd1) && input_ge1)  || (ge2_free && (fifo_wrptr_plus1== 4'd1) && input_ge2)  ||(ge3_free && (fifo_wrptr_plus2== 4'd1) && input_ge3);
  always @(posedge clk or negedge reset_n)
    begin
      if (reset_n == 0)
          fifo_1 <= 0;
      else if (fifo_1_enable)
          fifo_1 <= fifo_1_mux;
    end


  assign fifo_1_mux = (((fifo_wrptr == 4'd1) && itm_valid))? itm :
    (((fifo_wrptr == 4'd1) && atm_valid))? overflow_pending_atm :
    (((fifo_wrptr == 4'd1) && dtm_valid))? overflow_pending_dtm :
    (((fifo_wrptr_plus1 == 4'd1) && (ge2_free & itm_valid & atm_valid)))? overflow_pending_atm :
    (((fifo_wrptr_plus1 == 4'd1) && (ge2_free & itm_valid & dtm_valid)))? overflow_pending_dtm :
    (((fifo_wrptr_plus1 == 4'd1) && (ge2_free & atm_valid & dtm_valid)))? overflow_pending_dtm :
    overflow_pending_dtm;

  assign fifo_2_enable = ((fifo_wrptr == 4'd2) && input_ge1)  || (ge2_free && (fifo_wrptr_plus1== 4'd2) && input_ge2)  ||(ge3_free && (fifo_wrptr_plus2== 4'd2) && input_ge3);
  always @(posedge clk or negedge reset_n)
    begin
      if (reset_n == 0)
          fifo_2 <= 0;
      else if (fifo_2_enable)
          fifo_2 <= fifo_2_mux;
    end


  assign fifo_2_mux = (((fifo_wrptr == 4'd2) && itm_valid))? itm :
    (((fifo_wrptr == 4'd2) && atm_valid))? overflow_pending_atm :
    (((fifo_wrptr == 4'd2) && dtm_valid))? overflow_pending_dtm :
    (((fifo_wrptr_plus1 == 4'd2) && (ge2_free & itm_valid & atm_valid)))? overflow_pending_atm :
    (((fifo_wrptr_plus1 == 4'd2) && (ge2_free & itm_valid & dtm_valid)))? overflow_pending_dtm :
    (((fifo_wrptr_plus1 == 4'd2) && (ge2_free & atm_valid & dtm_valid)))? overflow_pending_dtm :
    overflow_pending_dtm;

  assign fifo_3_enable = ((fifo_wrptr == 4'd3) && input_ge1)  || (ge2_free && (fifo_wrptr_plus1== 4'd3) && input_ge2)  ||(ge3_free && (fifo_wrptr_plus2== 4'd3) && input_ge3);
  always @(posedge clk or negedge reset_n)
    begin
      if (reset_n == 0)
          fifo_3 <= 0;
      else if (fifo_3_enable)
          fifo_3 <= fifo_3_mux;
    end


  assign fifo_3_mux = (((fifo_wrptr == 4'd3) && itm_valid))? itm :
    (((fifo_wrptr == 4'd3) && atm_valid))? overflow_pending_atm :
    (((fifo_wrptr == 4'd3) && dtm_valid))? overflow_pending_dtm :
    (((fifo_wrptr_plus1 == 4'd3) && (ge2_free & itm_valid & atm_valid)))? overflow_pending_atm :
    (((fifo_wrptr_plus1 == 4'd3) && (ge2_free & itm_valid & dtm_valid)))? overflow_pending_dtm :
    (((fifo_wrptr_plus1 == 4'd3) && (ge2_free & atm_valid & dtm_valid)))? overflow_pending_dtm :
    overflow_pending_dtm;

  assign fifo_4_enable = ((fifo_wrptr == 4'd4) && input_ge1)  || (ge2_free && (fifo_wrptr_plus1== 4'd4) && input_ge2)  ||(ge3_free && (fifo_wrptr_plus2== 4'd4) && input_ge3);
  always @(posedge clk or negedge reset_n)
    begin
      if (reset_n == 0)
          fifo_4 <= 0;
      else if (fifo_4_enable)
          fifo_4 <= fifo_4_mux;
    end


  assign fifo_4_mux = (((fifo_wrptr == 4'd4) && itm_valid))? itm :
    (((fifo_wrptr == 4'd4) && atm_valid))? overflow_pending_atm :
    (((fifo_wrptr == 4'd4) && dtm_valid))? overflow_pending_dtm :
    (((fifo_wrptr_plus1 == 4'd4) && (ge2_free & itm_valid & atm_valid)))? overflow_pending_atm :
    (((fifo_wrptr_plus1 == 4'd4) && (ge2_free & itm_valid & dtm_valid)))? overflow_pending_dtm :
    (((fifo_wrptr_plus1 == 4'd4) && (ge2_free & atm_valid & dtm_valid)))? overflow_pending_dtm :
    overflow_pending_dtm;

  assign fifo_5_enable = ((fifo_wrptr == 4'd5) && input_ge1)  || (ge2_free && (fifo_wrptr_plus1== 4'd5) && input_ge2)  ||(ge3_free && (fifo_wrptr_plus2== 4'd5) && input_ge3);
  always @(posedge clk or negedge reset_n)
    begin
      if (reset_n == 0)
          fifo_5 <= 0;
      else if (fifo_5_enable)
          fifo_5 <= fifo_5_mux;
    end


  assign fifo_5_mux = (((fifo_wrptr == 4'd5) && itm_valid))? itm :
    (((fifo_wrptr == 4'd5) && atm_valid))? overflow_pending_atm :
    (((fifo_wrptr == 4'd5) && dtm_valid))? overflow_pending_dtm :
    (((fifo_wrptr_plus1 == 4'd5) && (ge2_free & itm_valid & atm_valid)))? overflow_pending_atm :
    (((fifo_wrptr_plus1 == 4'd5) && (ge2_free & itm_valid & dtm_valid)))? overflow_pending_dtm :
    (((fifo_wrptr_plus1 == 4'd5) && (ge2_free & atm_valid & dtm_valid)))? overflow_pending_dtm :
    overflow_pending_dtm;

  assign fifo_6_enable = ((fifo_wrptr == 4'd6) && input_ge1)  || (ge2_free && (fifo_wrptr_plus1== 4'd6) && input_ge2)  ||(ge3_free && (fifo_wrptr_plus2== 4'd6) && input_ge3);
  always @(posedge clk or negedge reset_n)
    begin
      if (reset_n == 0)
          fifo_6 <= 0;
      else if (fifo_6_enable)
          fifo_6 <= fifo_6_mux;
    end


  assign fifo_6_mux = (((fifo_wrptr == 4'd6) && itm_valid))? itm :
    (((fifo_wrptr == 4'd6) && atm_valid))? overflow_pending_atm :
    (((fifo_wrptr == 4'd6) && dtm_valid))? overflow_pending_dtm :
    (((fifo_wrptr_plus1 == 4'd6) && (ge2_free & itm_valid & atm_valid)))? overflow_pending_atm :
    (((fifo_wrptr_plus1 == 4'd6) && (ge2_free & itm_valid & dtm_valid)))? overflow_pending_dtm :
    (((fifo_wrptr_plus1 == 4'd6) && (ge2_free & atm_valid & dtm_valid)))? overflow_pending_dtm :
    overflow_pending_dtm;

  assign fifo_7_enable = ((fifo_wrptr == 4'd7) && input_ge1)  || (ge2_free && (fifo_wrptr_plus1== 4'd7) && input_ge2)  ||(ge3_free && (fifo_wrptr_plus2== 4'd7) && input_ge3);
  always @(posedge clk or negedge reset_n)
    begin
      if (reset_n == 0)
          fifo_7 <= 0;
      else if (fifo_7_enable)
          fifo_7 <= fifo_7_mux;
    end


  assign fifo_7_mux = (((fifo_wrptr == 4'd7) && itm_valid))? itm :
    (((fifo_wrptr == 4'd7) && atm_valid))? overflow_pending_atm :
    (((fifo_wrptr == 4'd7) && dtm_valid))? overflow_pending_dtm :
    (((fifo_wrptr_plus1 == 4'd7) && (ge2_free & itm_valid & atm_valid)))? overflow_pending_atm :
    (((fifo_wrptr_plus1 == 4'd7) && (ge2_free & itm_valid & dtm_valid)))? overflow_pending_dtm :
    (((fifo_wrptr_plus1 == 4'd7) && (ge2_free & atm_valid & dtm_valid)))? overflow_pending_dtm :
    overflow_pending_dtm;

  assign fifo_8_enable = ((fifo_wrptr == 4'd8) && input_ge1)  || (ge2_free && (fifo_wrptr_plus1== 4'd8) && input_ge2)  ||(ge3_free && (fifo_wrptr_plus2== 4'd8) && input_ge3);
  always @(posedge clk or negedge reset_n)
    begin
      if (reset_n == 0)
          fifo_8 <= 0;
      else if (fifo_8_enable)
          fifo_8 <= fifo_8_mux;
    end


  assign fifo_8_mux = (((fifo_wrptr == 4'd8) && itm_valid))? itm :
    (((fifo_wrptr == 4'd8) && atm_valid))? overflow_pending_atm :
    (((fifo_wrptr == 4'd8) && dtm_valid))? overflow_pending_dtm :
    (((fifo_wrptr_plus1 == 4'd8) && (ge2_free & itm_valid & atm_valid)))? overflow_pending_atm :
    (((fifo_wrptr_plus1 == 4'd8) && (ge2_free & itm_valid & dtm_valid)))? overflow_pending_dtm :
    (((fifo_wrptr_plus1 == 4'd8) && (ge2_free & atm_valid & dtm_valid)))? overflow_pending_dtm :
    overflow_pending_dtm;

  assign fifo_9_enable = ((fifo_wrptr == 4'd9) && input_ge1)  || (ge2_free && (fifo_wrptr_plus1== 4'd9) && input_ge2)  ||(ge3_free && (fifo_wrptr_plus2== 4'd9) && input_ge3);
  always @(posedge clk or negedge reset_n)
    begin
      if (reset_n == 0)
          fifo_9 <= 0;
      else if (fifo_9_enable)
          fifo_9 <= fifo_9_mux;
    end


  assign fifo_9_mux = (((fifo_wrptr == 4'd9) && itm_valid))? itm :
    (((fifo_wrptr == 4'd9) && atm_valid))? overflow_pending_atm :
    (((fifo_wrptr == 4'd9) && dtm_valid))? overflow_pending_dtm :
    (((fifo_wrptr_plus1 == 4'd9) && (ge2_free & itm_valid & atm_valid)))? overflow_pending_atm :
    (((fifo_wrptr_plus1 == 4'd9) && (ge2_free & itm_valid & dtm_valid)))? overflow_pending_dtm :
    (((fifo_wrptr_plus1 == 4'd9) && (ge2_free & atm_valid & dtm_valid)))? overflow_pending_dtm :
    overflow_pending_dtm;

  assign fifo_10_enable = ((fifo_wrptr == 4'd10) && input_ge1)  || (ge2_free && (fifo_wrptr_plus1== 4'd10) && input_ge2)  ||(ge3_free && (fifo_wrptr_plus2== 4'd10) && input_ge3);
  always @(posedge clk or negedge reset_n)
    begin
      if (reset_n == 0)
          fifo_10 <= 0;
      else if (fifo_10_enable)
          fifo_10 <= fifo_10_mux;
    end


  assign fifo_10_mux = (((fifo_wrptr == 4'd10) && itm_valid))? itm :
    (((fifo_wrptr == 4'd10) && atm_valid))? overflow_pending_atm :
    (((fifo_wrptr == 4'd10) && dtm_valid))? overflow_pending_dtm :
    (((fifo_wrptr_plus1 == 4'd10) && (ge2_free & itm_valid & atm_valid)))? overflow_pending_atm :
    (((fifo_wrptr_plus1 == 4'd10) && (ge2_free & itm_valid & dtm_valid)))? overflow_pending_dtm :
    (((fifo_wrptr_plus1 == 4'd10) && (ge2_free & atm_valid & dtm_valid)))? overflow_pending_dtm :
    overflow_pending_dtm;

  assign fifo_11_enable = ((fifo_wrptr == 4'd11) && input_ge1)  || (ge2_free && (fifo_wrptr_plus1== 4'd11) && input_ge2)  ||(ge3_free && (fifo_wrptr_plus2== 4'd11) && input_ge3);
  always @(posedge clk or negedge reset_n)
    begin
      if (reset_n == 0)
          fifo_11 <= 0;
      else if (fifo_11_enable)
          fifo_11 <= fifo_11_mux;
    end


  assign fifo_11_mux = (((fifo_wrptr == 4'd11) && itm_valid))? itm :
    (((fifo_wrptr == 4'd11) && atm_valid))? overflow_pending_atm :
    (((fifo_wrptr == 4'd11) && dtm_valid))? overflow_pending_dtm :
    (((fifo_wrptr_plus1 == 4'd11) && (ge2_free & itm_valid & atm_valid)))? overflow_pending_atm :
    (((fifo_wrptr_plus1 == 4'd11) && (ge2_free & itm_valid & dtm_valid)))? overflow_pending_dtm :
    (((fifo_wrptr_plus1 == 4'd11) && (ge2_free & atm_valid & dtm_valid)))? overflow_pending_dtm :
    overflow_pending_dtm;

  assign fifo_12_enable = ((fifo_wrptr == 4'd12) && input_ge1)  || (ge2_free && (fifo_wrptr_plus1== 4'd12) && input_ge2)  ||(ge3_free && (fifo_wrptr_plus2== 4'd12) && input_ge3);
  always @(posedge clk or negedge reset_n)
    begin
      if (reset_n == 0)
          fifo_12 <= 0;
      else if (fifo_12_enable)
          fifo_12 <= fifo_12_mux;
    end


  assign fifo_12_mux = (((fifo_wrptr == 4'd12) && itm_valid))? itm :
    (((fifo_wrptr == 4'd12) && atm_valid))? overflow_pending_atm :
    (((fifo_wrptr == 4'd12) && dtm_valid))? overflow_pending_dtm :
    (((fifo_wrptr_plus1 == 4'd12) && (ge2_free & itm_valid & atm_valid)))? overflow_pending_atm :
    (((fifo_wrptr_plus1 == 4'd12) && (ge2_free & itm_valid & dtm_valid)))? overflow_pending_dtm :
    (((fifo_wrptr_plus1 == 4'd12) && (ge2_free & atm_valid & dtm_valid)))? overflow_pending_dtm :
    overflow_pending_dtm;

  assign fifo_13_enable = ((fifo_wrptr == 4'd13) && input_ge1)  || (ge2_free && (fifo_wrptr_plus1== 4'd13) && input_ge2)  ||(ge3_free && (fifo_wrptr_plus2== 4'd13) && input_ge3);
  always @(posedge clk or negedge reset_n)
    begin
      if (reset_n == 0)
          fifo_13 <= 0;
      else if (fifo_13_enable)
          fifo_13 <= fifo_13_mux;
    end


  assign fifo_13_mux = (((fifo_wrptr == 4'd13) && itm_valid))? itm :
    (((fifo_wrptr == 4'd13) && atm_valid))? overflow_pending_atm :
    (((fifo_wrptr == 4'd13) && dtm_valid))? overflow_pending_dtm :
    (((fifo_wrptr_plus1 == 4'd13) && (ge2_free & itm_valid & atm_valid)))? overflow_pending_atm :
    (((fifo_wrptr_plus1 == 4'd13) && (ge2_free & itm_valid & dtm_valid)))? overflow_pending_dtm :
    (((fifo_wrptr_plus1 == 4'd13) && (ge2_free & atm_valid & dtm_valid)))? overflow_pending_dtm :
    overflow_pending_dtm;

  assign fifo_14_enable = ((fifo_wrptr == 4'd14) && input_ge1)  || (ge2_free && (fifo_wrptr_plus1== 4'd14) && input_ge2)  ||(ge3_free && (fifo_wrptr_plus2== 4'd14) && input_ge3);
  always @(posedge clk or negedge reset_n)
    begin
      if (reset_n == 0)
          fifo_14 <= 0;
      else if (fifo_14_enable)
          fifo_14 <= fifo_14_mux;
    end


  assign fifo_14_mux = (((fifo_wrptr == 4'd14) && itm_valid))? itm :
    (((fifo_wrptr == 4'd14) && atm_valid))? overflow_pending_atm :
    (((fifo_wrptr == 4'd14) && dtm_valid))? overflow_pending_dtm :
    (((fifo_wrptr_plus1 == 4'd14) && (ge2_free & itm_valid & atm_valid)))? overflow_pending_atm :
    (((fifo_wrptr_plus1 == 4'd14) && (ge2_free & itm_valid & dtm_valid)))? overflow_pending_dtm :
    (((fifo_wrptr_plus1 == 4'd14) && (ge2_free & atm_valid & dtm_valid)))? overflow_pending_dtm :
    overflow_pending_dtm;

  assign fifo_15_enable = ((fifo_wrptr == 4'd15) && input_ge1)  || (ge2_free && (fifo_wrptr_plus1== 4'd15) && input_ge2)  ||(ge3_free && (fifo_wrptr_plus2== 4'd15) && input_ge3);
  always @(posedge clk or negedge reset_n)
    begin
      if (reset_n == 0)
          fifo_15 <= 0;
      else if (fifo_15_enable)
          fifo_15 <= fifo_15_mux;
    end


  assign fifo_15_mux = (((fifo_wrptr == 4'd15) && itm_valid))? itm :
    (((fifo_wrptr == 4'd15) && atm_valid))? overflow_pending_atm :
    (((fifo_wrptr == 4'd15) && dtm_valid))? overflow_pending_dtm :
    (((fifo_wrptr_plus1 == 4'd15) && (ge2_free & itm_valid & atm_valid)))? overflow_pending_atm :
    (((fifo_wrptr_plus1 == 4'd15) && (ge2_free & itm_valid & dtm_valid)))? overflow_pending_dtm :
    (((fifo_wrptr_plus1 == 4'd15) && (ge2_free & atm_valid & dtm_valid)))? overflow_pending_dtm :
    overflow_pending_dtm;

  assign input_ge1 = |input_tm_cnt;
  assign input_ge2 = input_tm_cnt[1];
  assign input_ge3 = &input_tm_cnt;
  assign overflow_pending_atm = {overflow_pending, atm[34 : 0]};
  assign overflow_pending_dtm = {overflow_pending, dtm[34 : 0]};
  assign fifo_read_mux = (fifo_rdptr == 4'd0)? fifo_0 :
    (fifo_rdptr == 4'd1)? fifo_1 :
    (fifo_rdptr == 4'd2)? fifo_2 :
    (fifo_rdptr == 4'd3)? fifo_3 :
    (fifo_rdptr == 4'd4)? fifo_4 :
    (fifo_rdptr == 4'd5)? fifo_5 :
    (fifo_rdptr == 4'd6)? fifo_6 :
    (fifo_rdptr == 4'd7)? fifo_7 :
    (fifo_rdptr == 4'd8)? fifo_8 :
    (fifo_rdptr == 4'd9)? fifo_9 :
    (fifo_rdptr == 4'd10)? fifo_10 :
    (fifo_rdptr == 4'd11)? fifo_11 :
    (fifo_rdptr == 4'd12)? fifo_12 :
    (fifo_rdptr == 4'd13)? fifo_13 :
    (fifo_rdptr == 4'd14)? fifo_14 :
    fifo_15;


endmodule


// synthesis translate_off
`timescale 1ns / 1ps
// synthesis translate_on

// turn off superfluous verilog processor warnings 
// altera message_level Level1 
// altera message_off 10034 10035 10036 10037 10230 10240 10030 

module snes_tst_cpu_nios2_gen2_0_cpu_nios2_oci_pib (
                                                     // outputs:
                                                      tr_data
                                                   )
;

  output  [ 35: 0] tr_data;


wire    [ 35: 0] tr_data;
  assign tr_data = 0;

endmodule


// synthesis translate_off
`timescale 1ns / 1ps
// synthesis translate_on

// turn off superfluous verilog processor warnings 
// altera message_level Level1 
// altera message_off 10034 10035 10036 10037 10230 10240 10030 

module snes_tst_cpu_nios2_gen2_0_cpu_nios2_oci_im (
                                                    // inputs:
                                                     clk,
                                                     jrst_n,
                                                     trc_ctrl,
                                                     tw,

                                                    // outputs:
                                                     tracemem_on,
                                                     tracemem_trcdata,
                                                     tracemem_tw,
                                                     trc_im_addr,
                                                     trc_wrap,
                                                     xbrk_wrap_traceoff
                                                  )
;

  output           tracemem_on;
  output  [ 35: 0] tracemem_trcdata;
  output           tracemem_tw;
  output  [  6: 0] trc_im_addr;
  output           trc_wrap;
  output           xbrk_wrap_traceoff;
  input            clk;
  input            jrst_n;
  input   [ 15: 0] trc_ctrl;
  input   [ 35: 0] tw;


wire             tracemem_on;
wire    [ 35: 0] tracemem_trcdata;
wire             tracemem_tw;
reg     [  6: 0] trc_im_addr /* synthesis ALTERA_ATTRIBUTE = "SUPPRESS_DA_RULE_INTERNAL=\"D101,D103,R101\""  */;
wire    [ 35: 0] trc_im_data;
wire             trc_on_chip;
reg              trc_wrap /* synthesis ALTERA_ATTRIBUTE = "SUPPRESS_DA_RULE_INTERNAL=\"D101,D103,R101\""  */;
wire             tw_valid;
wire             xbrk_wrap_traceoff;
  assign trc_im_data = tw;
  always @(posedge clk or negedge jrst_n)
    begin
      if (jrst_n == 0)
        begin
          trc_im_addr <= 0;
          trc_wrap <= 0;
        end
      else 
        begin
          trc_im_addr <= 0;
          trc_wrap <= 0;
        end
    end


  assign trc_on_chip = ~trc_ctrl[8];
  assign tw_valid = |trc_im_data[35 : 32];
  assign xbrk_wrap_traceoff = trc_ctrl[10] & trc_wrap;
  assign tracemem_trcdata = 0;

endmodule


// synthesis translate_off
`timescale 1ns / 1ps
// synthesis translate_on

// turn off superfluous verilog processor warnings 
// altera message_level Level1 
// altera message_off 10034 10035 10036 10037 10230 10240 10030 

module snes_tst_cpu_nios2_gen2_0_cpu_nios2_performance_monitors 
;




endmodule


// synthesis translate_off
`timescale 1ns / 1ps
// synthesis translate_on

// turn off superfluous verilog processor warnings 
// altera message_level Level1 
// altera message_off 10034 10035 10036 10037 10230 10240 10030 

module snes_tst_cpu_nios2_gen2_0_cpu_nios2_avalon_reg (
                                                        // inputs:
                                                         address,
                                                         clk,
                                                         debugaccess,
                                                         monitor_error,
                                                         monitor_go,
                                                         monitor_ready,
                                                         reset_n,
                                                         write,
                                                         writedata,

                                                        // outputs:
                                                         oci_ienable,
                                                         oci_reg_readdata,
                                                         oci_single_step_mode,
                                                         ocireg_ers,
                                                         ocireg_mrs,
                                                         take_action_ocireg
                                                      )
;

  output  [ 31: 0] oci_ienable;
  output  [ 31: 0] oci_reg_readdata;
  output           oci_single_step_mode;
  output           ocireg_ers;
  output           ocireg_mrs;
  output           take_action_ocireg;
  input   [  8: 0] address;
  input            clk;
  input            debugaccess;
  input            monitor_error;
  input            monitor_go;
  input            monitor_ready;
  input            reset_n;
  input            write;
  input   [ 31: 0] writedata;


reg     [ 31: 0] oci_ienable;
wire             oci_reg_00_addressed;
wire             oci_reg_01_addressed;
wire    [ 31: 0] oci_reg_readdata;
reg              oci_single_step_mode;
wire             ocireg_ers;
wire             ocireg_mrs;
wire             ocireg_sstep;
wire             take_action_oci_intr_mask_reg;
wire             take_action_ocireg;
wire             write_strobe;
  assign oci_reg_00_addressed = address == 9'h100;
  assign oci_reg_01_addressed = address == 9'h101;
  assign write_strobe = write & debugaccess;
  assign take_action_ocireg = write_strobe & oci_reg_00_addressed;
  assign take_action_oci_intr_mask_reg = write_strobe & oci_reg_01_addressed;
  assign ocireg_ers = writedata[1];
  assign ocireg_mrs = writedata[0];
  assign ocireg_sstep = writedata[3];
  assign oci_reg_readdata = oci_reg_00_addressed ? {28'b0, oci_single_step_mode, monitor_go,
    monitor_ready, monitor_error} : 
    oci_reg_01_addressed ?  oci_ienable :   
    32'b0;

  always @(posedge clk or negedge reset_n)
    begin
      if (reset_n == 0)
          oci_single_step_mode <= 1'b0;
      else if (take_action_ocireg)
          oci_single_step_mode <= ocireg_sstep;
    end


  always @(posedge clk or negedge reset_n)
    begin
      if (reset_n == 0)
          oci_ienable <= 32'b00000000000000000000000000000001;
      else if (take_action_oci_intr_mask_reg)
          oci_ienable <= writedata | ~(32'b00000000000000000000000000000001);
    end



endmodule


// synthesis translate_off
`timescale 1ns / 1ps
// synthesis translate_on

// turn off superfluous verilog processor warnings 
// altera message_level Level1 
// altera message_off 10034 10035 10036 10037 10230 10240 10030 

module snes_tst_cpu_nios2_gen2_0_cpu_ociram_sp_ram_module (
                                                            // inputs:
                                                             address,
                                                             byteenable,
                                                             clock,
                                                             data,
                                                             reset_req,
                                                             wren,

                                                            // outputs:
                                                             q
                                                          )
;

  parameter lpm_file = "UNUSED";


  output  [ 31: 0] q;
  input   [  7: 0] address;
  input   [  3: 0] byteenable;
  input            clock;
  input   [ 31: 0] data;
  input            reset_req;
  input            wren;


wire             clocken;
wire    [ 31: 0] q;
wire    [ 31: 0] ram_q;
  assign q = ram_q;
  assign clocken = ~reset_req;
  altsyncram the_altsyncram
    (
      .address_a (address),
      .byteena_a (byteenable),
      .clock0 (clock),
      .clocken0 (clocken),
      .data_a (data),
      .q_a (ram_q),
      .wren_a (wren)
    );

  defparam the_altsyncram.init_file = lpm_file,
           the_altsyncram.maximum_depth = 0,
           the_altsyncram.numwords_a = 256,
           the_altsyncram.operation_mode = "SINGLE_PORT",
           the_altsyncram.outdata_reg_a = "UNREGISTERED",
           the_altsyncram.ram_block_type = "AUTO",
           the_altsyncram.read_during_write_mode_port_a = "DONT_CARE",
           the_altsyncram.width_a = 32,
           the_altsyncram.width_byteena_a = 4,
           the_altsyncram.widthad_a = 8;


endmodule


// synthesis translate_off
`timescale 1ns / 1ps
// synthesis translate_on

// turn off superfluous verilog processor warnings 
// altera message_level Level1 
// altera message_off 10034 10035 10036 10037 10230 10240 10030 

module snes_tst_cpu_nios2_gen2_0_cpu_nios2_ocimem (
                                                    // inputs:
                                                     address,
                                                     byteenable,
                                                     clk,
                                                     debugaccess,
                                                     jdo,
                                                     jrst_n,
                                                     read,
                                                     reset_req,
                                                     take_action_ocimem_a,
                                                     take_action_ocimem_b,
                                                     take_no_action_ocimem_a,
                                                     write,
                                                     writedata,

                                                    // outputs:
                                                     MonDReg,
                                                     ociram_readdata,
                                                     waitrequest
                                                  )
;

  output  [ 31: 0] MonDReg;
  output  [ 31: 0] ociram_readdata;
  output           waitrequest;
  input   [  8: 0] address;
  input   [  3: 0] byteenable;
  input            clk;
  input            debugaccess;
  input   [ 37: 0] jdo;
  input            jrst_n;
  input            read;
  input            reset_req;
  input            take_action_ocimem_a;
  input            take_action_ocimem_b;
  input            take_no_action_ocimem_a;
  input            write;
  input   [ 31: 0] writedata;


reg     [ 10: 0] MonAReg /* synthesis ALTERA_ATTRIBUTE = "SUPPRESS_DA_RULE_INTERNAL=\"D101,D103,R101\""  */;
wire    [  8: 0] MonARegAddrInc;
wire             MonARegAddrIncAccessingRAM;
reg     [ 31: 0] MonDReg /* synthesis ALTERA_ATTRIBUTE = "SUPPRESS_DA_RULE_INTERNAL=\"D101,D103,R101\""  */;
reg              avalon_ociram_readdata_ready /* synthesis ALTERA_ATTRIBUTE = "SUPPRESS_DA_RULE_INTERNAL=\"D101,D103,R101\""  */;
wire             avalon_ram_wr;
wire    [ 31: 0] cfgrom_readdata;
reg              jtag_ram_access /* synthesis ALTERA_ATTRIBUTE = "SUPPRESS_DA_RULE_INTERNAL=\"D101,D103,R101\""  */;
reg              jtag_ram_rd /* synthesis ALTERA_ATTRIBUTE = "SUPPRESS_DA_RULE_INTERNAL=\"D101,D103,R101\""  */;
reg              jtag_ram_rd_d1 /* synthesis ALTERA_ATTRIBUTE = "SUPPRESS_DA_RULE_INTERNAL=\"D101,D103,R101\""  */;
reg              jtag_ram_wr /* synthesis ALTERA_ATTRIBUTE = "SUPPRESS_DA_RULE_INTERNAL=\"D101,D103,R101\""  */;
reg              jtag_rd /* synthesis ALTERA_ATTRIBUTE = "SUPPRESS_DA_RULE_INTERNAL=\"D101,D103,R101\""  */;
reg              jtag_rd_d1 /* synthesis ALTERA_ATTRIBUTE = "SUPPRESS_DA_RULE_INTERNAL=\"D101,D103,R101\""  */;
wire    [  7: 0] ociram_addr;
wire    [  3: 0] ociram_byteenable;
wire    [ 31: 0] ociram_readdata;
wire             ociram_reset_req;
wire    [ 31: 0] ociram_wr_data;
wire             ociram_wr_en;
reg              waitrequest /* synthesis ALTERA_ATTRIBUTE = "SUPPRESS_DA_RULE_INTERNAL=\"D101,D103,R101\""  */;
  always @(posedge clk or negedge jrst_n)
    begin
      if (jrst_n == 0)
        begin
          jtag_rd <= 1'b0;
          jtag_rd_d1 <= 1'b0;
          jtag_ram_wr <= 1'b0;
          jtag_ram_rd <= 1'b0;
          jtag_ram_rd_d1 <= 1'b0;
          jtag_ram_access <= 1'b0;
          MonAReg <= 0;
          MonDReg <= 0;
          waitrequest <= 1'b1;
          avalon_ociram_readdata_ready <= 1'b0;
        end
      else 
        begin
          if (take_no_action_ocimem_a)
            begin
              MonAReg[10 : 2] <= MonARegAddrInc;
              jtag_rd <= 1'b1;
              jtag_ram_rd <= MonARegAddrIncAccessingRAM;
              jtag_ram_access <= MonARegAddrIncAccessingRAM;
            end
          else if (take_action_ocimem_a)
            begin
              MonAReg[10 : 2] <= { jdo[17],
                            jdo[33 : 26] };

              jtag_rd <= 1'b1;
              jtag_ram_rd <= ~jdo[17];
              jtag_ram_access <= ~jdo[17];
            end
          else if (take_action_ocimem_b)
            begin
              MonAReg[10 : 2] <= MonARegAddrInc;
              MonDReg <= jdo[34 : 3];
              jtag_ram_wr <= MonARegAddrIncAccessingRAM;
              jtag_ram_access <= MonARegAddrIncAccessingRAM;
            end
          else 
            begin
              jtag_rd <= 0;
              jtag_ram_wr <= 0;
              jtag_ram_rd <= 0;
              jtag_ram_access <= 0;
              if (jtag_rd_d1)
                  MonDReg <= jtag_ram_rd_d1 ? ociram_readdata : cfgrom_readdata;
            end
          jtag_rd_d1 <= jtag_rd;
          jtag_ram_rd_d1 <= jtag_ram_rd;
          if (~waitrequest)
            begin
              waitrequest <= 1'b1;
              avalon_ociram_readdata_ready <= 1'b0;
            end
          else if (write)
              waitrequest <= ~address[8] & jtag_ram_access;
          else if (read)
            begin
              avalon_ociram_readdata_ready <= ~(~address[8] & jtag_ram_access);
              waitrequest <= ~avalon_ociram_readdata_ready;
            end
          else 
            begin
              waitrequest <= 1'b1;
              avalon_ociram_readdata_ready <= 1'b0;
            end
        end
    end


  assign MonARegAddrInc = MonAReg[10 : 2]+1;
  assign MonARegAddrIncAccessingRAM = ~MonARegAddrInc[8];
  assign avalon_ram_wr = write & ~address[8] & debugaccess;
  assign ociram_addr = jtag_ram_access ? MonAReg[9 : 2] : address[7 : 0];
  assign ociram_wr_data = jtag_ram_access ? MonDReg[31 : 0] : writedata;
  assign ociram_byteenable = jtag_ram_access ? 4'b1111 : byteenable;
  assign ociram_wr_en = jtag_ram_access ? jtag_ram_wr : avalon_ram_wr;
  assign ociram_reset_req = reset_req & ~jtag_ram_access;
//snes_tst_cpu_nios2_gen2_0_cpu_ociram_sp_ram, which is an nios_sp_ram
snes_tst_cpu_nios2_gen2_0_cpu_ociram_sp_ram_module snes_tst_cpu_nios2_gen2_0_cpu_ociram_sp_ram
  (
    .address    (ociram_addr),
    .byteenable (ociram_byteenable),
    .clock      (clk),
    .data       (ociram_wr_data),
    .q          (ociram_readdata),
    .reset_req  (ociram_reset_req),
    .wren       (ociram_wr_en)
  );

//synthesis translate_off
`ifdef NO_PLI
defparam snes_tst_cpu_nios2_gen2_0_cpu_ociram_sp_ram.lpm_file = "snes_tst_cpu_nios2_gen2_0_cpu_ociram_default_contents.dat";
`else
defparam snes_tst_cpu_nios2_gen2_0_cpu_ociram_sp_ram.lpm_file = "snes_tst_cpu_nios2_gen2_0_cpu_ociram_default_contents.hex";
`endif
//synthesis translate_on
  assign cfgrom_readdata = (MonAReg[4 : 2] == 3'd0)? 32'h00000020 :
    (MonAReg[4 : 2] == 3'd1)? 32'h00001414 :
    (MonAReg[4 : 2] == 3'd2)? 32'h00040000 :
    (MonAReg[4 : 2] == 3'd3)? 32'h00000100 :
    (MonAReg[4 : 2] == 3'd4)? 32'h20000000 :
    (MonAReg[4 : 2] == 3'd5)? 32'h00000000 :
    (MonAReg[4 : 2] == 3'd6)? 32'h00000000 :
    32'h00000000;


endmodule


// synthesis translate_off
`timescale 1ns / 1ps
// synthesis translate_on

// turn off superfluous verilog processor warnings 
// altera message_level Level1 
// altera message_off 10034 10035 10036 10037 10230 10240 10030 

module snes_tst_cpu_nios2_gen2_0_cpu_nios2_oci (
                                                 // inputs:
                                                  D_valid,
                                                  E_st_data,
                                                  E_valid,
                                                  F_pc,
                                                  address_nxt,
                                                  av_ld_data_aligned_filtered,
                                                  byteenable_nxt,
                                                  clk,
                                                  d_address,
                                                  d_read,
                                                  d_waitrequest,
                                                  d_write,
                                                  debugaccess_nxt,
                                                  hbreak_enabled,
                                                  read_nxt,
                                                  reset,
                                                  reset_n,
                                                  reset_req,
                                                  write_nxt,
                                                  writedata_nxt,

                                                 // outputs:
                                                  debug_mem_slave_debugaccess_to_roms,
                                                  oci_hbreak_req,
                                                  oci_ienable,
                                                  oci_single_step_mode,
                                                  readdata,
                                                  resetrequest,
                                                  waitrequest
                                               )
;

  output           debug_mem_slave_debugaccess_to_roms;
  output           oci_hbreak_req;
  output  [ 31: 0] oci_ienable;
  output           oci_single_step_mode;
  output  [ 31: 0] readdata;
  output           resetrequest;
  output           waitrequest;
  input            D_valid;
  input   [ 31: 0] E_st_data;
  input            E_valid;
  input   [ 17: 0] F_pc;
  input   [  8: 0] address_nxt;
  input   [ 31: 0] av_ld_data_aligned_filtered;
  input   [  3: 0] byteenable_nxt;
  input            clk;
  input   [ 19: 0] d_address;
  input            d_read;
  input            d_waitrequest;
  input            d_write;
  input            debugaccess_nxt;
  input            hbreak_enabled;
  input            read_nxt;
  input            reset;
  input            reset_n;
  input            reset_req;
  input            write_nxt;
  input   [ 31: 0] writedata_nxt;


wire    [ 31: 0] MonDReg;
reg     [  8: 0] address;
wire    [ 35: 0] atm;
wire    [ 31: 0] break_readreg;
reg     [  3: 0] byteenable;
wire    [ 19: 0] cpu_d_address;
wire             cpu_d_read;
wire    [ 31: 0] cpu_d_readdata;
wire             cpu_d_wait;
wire             cpu_d_write;
wire    [ 31: 0] cpu_d_writedata;
wire             dbrk_break;
wire             dbrk_goto0;
wire             dbrk_goto1;
wire             dbrk_hit0_latch;
wire             dbrk_hit1_latch;
wire             dbrk_hit2_latch;
wire             dbrk_hit3_latch;
wire             dbrk_traceme;
wire             dbrk_traceoff;
wire             dbrk_traceon;
wire             dbrk_trigout;
wire             debug_mem_slave_debugaccess_to_roms;
reg              debugaccess;
wire             debugack;
wire             debugreq;
wire    [ 35: 0] dtm;
wire             dummy_sink;
wire    [ 35: 0] itm;
wire    [ 37: 0] jdo;
wire             jrst_n;
wire             monitor_error;
wire             monitor_go;
wire             monitor_ready;
wire             oci_hbreak_req;
wire    [ 31: 0] oci_ienable;
wire    [ 31: 0] oci_reg_readdata;
wire             oci_single_step_mode;
wire    [ 31: 0] ociram_readdata;
wire             ocireg_ers;
wire             ocireg_mrs;
reg              read;
reg     [ 31: 0] readdata;
wire             resetlatch;
wire             resetrequest;
wire             st_ready_test_idle;
wire             take_action_break_a;
wire             take_action_break_b;
wire             take_action_break_c;
wire             take_action_ocimem_a;
wire             take_action_ocimem_b;
wire             take_action_ocireg;
wire             take_action_tracectrl;
wire             take_no_action_break_a;
wire             take_no_action_break_b;
wire             take_no_action_break_c;
wire             take_no_action_ocimem_a;
wire    [ 35: 0] tr_data;
wire             tracemem_on;
wire    [ 35: 0] tracemem_trcdata;
wire             tracemem_tw;
wire    [ 15: 0] trc_ctrl;
wire    [  6: 0] trc_im_addr;
wire             trc_on;
wire             trc_wrap;
wire             trigbrktype;
wire             trigger_state_0;
wire             trigger_state_1;
wire             trigout;
wire    [ 35: 0] tw;
wire             waitrequest;
reg              write;
reg     [ 31: 0] writedata;
wire             xbrk_break;
wire    [  7: 0] xbrk_ctrl0;
wire    [  7: 0] xbrk_ctrl1;
wire    [  7: 0] xbrk_ctrl2;
wire    [  7: 0] xbrk_ctrl3;
wire             xbrk_goto0;
wire             xbrk_goto1;
wire             xbrk_traceoff;
wire             xbrk_traceon;
wire             xbrk_trigout;
wire             xbrk_wrap_traceoff;
  snes_tst_cpu_nios2_gen2_0_cpu_nios2_oci_debug the_snes_tst_cpu_nios2_gen2_0_cpu_nios2_oci_debug
    (
      .clk                  (clk),
      .dbrk_break           (dbrk_break),
      .debugack             (debugack),
      .debugreq             (debugreq),
      .hbreak_enabled       (hbreak_enabled),
      .jdo                  (jdo),
      .jrst_n               (jrst_n),
      .monitor_error        (monitor_error),
      .monitor_go           (monitor_go),
      .monitor_ready        (monitor_ready),
      .oci_hbreak_req       (oci_hbreak_req),
      .ocireg_ers           (ocireg_ers),
      .ocireg_mrs           (ocireg_mrs),
      .reset                (reset),
      .resetlatch           (resetlatch),
      .resetrequest         (resetrequest),
      .st_ready_test_idle   (st_ready_test_idle),
      .take_action_ocimem_a (take_action_ocimem_a),
      .take_action_ocireg   (take_action_ocireg),
      .xbrk_break           (xbrk_break)
    );

  snes_tst_cpu_nios2_gen2_0_cpu_nios2_oci_break the_snes_tst_cpu_nios2_gen2_0_cpu_nios2_oci_break
    (
      .break_readreg          (break_readreg),
      .clk                    (clk),
      .dbrk_break             (dbrk_break),
      .dbrk_goto0             (dbrk_goto0),
      .dbrk_goto1             (dbrk_goto1),
      .dbrk_hit0_latch        (dbrk_hit0_latch),
      .dbrk_hit1_latch        (dbrk_hit1_latch),
      .dbrk_hit2_latch        (dbrk_hit2_latch),
      .dbrk_hit3_latch        (dbrk_hit3_latch),
      .jdo                    (jdo),
      .jrst_n                 (jrst_n),
      .take_action_break_a    (take_action_break_a),
      .take_action_break_b    (take_action_break_b),
      .take_action_break_c    (take_action_break_c),
      .take_no_action_break_a (take_no_action_break_a),
      .take_no_action_break_b (take_no_action_break_b),
      .take_no_action_break_c (take_no_action_break_c),
      .trigbrktype            (trigbrktype),
      .trigger_state_0        (trigger_state_0),
      .trigger_state_1        (trigger_state_1),
      .xbrk_ctrl0             (xbrk_ctrl0),
      .xbrk_ctrl1             (xbrk_ctrl1),
      .xbrk_ctrl2             (xbrk_ctrl2),
      .xbrk_ctrl3             (xbrk_ctrl3),
      .xbrk_goto0             (xbrk_goto0),
      .xbrk_goto1             (xbrk_goto1)
    );

  snes_tst_cpu_nios2_gen2_0_cpu_nios2_oci_xbrk the_snes_tst_cpu_nios2_gen2_0_cpu_nios2_oci_xbrk
    (
      .D_valid         (D_valid),
      .E_valid         (E_valid),
      .F_pc            (F_pc),
      .clk             (clk),
      .reset_n         (reset_n),
      .trigger_state_0 (trigger_state_0),
      .trigger_state_1 (trigger_state_1),
      .xbrk_break      (xbrk_break),
      .xbrk_ctrl0      (xbrk_ctrl0),
      .xbrk_ctrl1      (xbrk_ctrl1),
      .xbrk_ctrl2      (xbrk_ctrl2),
      .xbrk_ctrl3      (xbrk_ctrl3),
      .xbrk_goto0      (xbrk_goto0),
      .xbrk_goto1      (xbrk_goto1),
      .xbrk_traceoff   (xbrk_traceoff),
      .xbrk_traceon    (xbrk_traceon),
      .xbrk_trigout    (xbrk_trigout)
    );

  snes_tst_cpu_nios2_gen2_0_cpu_nios2_oci_dbrk the_snes_tst_cpu_nios2_gen2_0_cpu_nios2_oci_dbrk
    (
      .E_st_data                   (E_st_data),
      .av_ld_data_aligned_filtered (av_ld_data_aligned_filtered),
      .clk                         (clk),
      .cpu_d_address               (cpu_d_address),
      .cpu_d_read                  (cpu_d_read),
      .cpu_d_readdata              (cpu_d_readdata),
      .cpu_d_wait                  (cpu_d_wait),
      .cpu_d_write                 (cpu_d_write),
      .cpu_d_writedata             (cpu_d_writedata),
      .d_address                   (d_address),
      .d_read                      (d_read),
      .d_waitrequest               (d_waitrequest),
      .d_write                     (d_write),
      .dbrk_break                  (dbrk_break),
      .dbrk_goto0                  (dbrk_goto0),
      .dbrk_goto1                  (dbrk_goto1),
      .dbrk_traceme                (dbrk_traceme),
      .dbrk_traceoff               (dbrk_traceoff),
      .dbrk_traceon                (dbrk_traceon),
      .dbrk_trigout                (dbrk_trigout),
      .debugack                    (debugack),
      .reset_n                     (reset_n)
    );

  snes_tst_cpu_nios2_gen2_0_cpu_nios2_oci_itrace the_snes_tst_cpu_nios2_gen2_0_cpu_nios2_oci_itrace
    (
      .clk                   (clk),
      .dbrk_traceoff         (dbrk_traceoff),
      .dbrk_traceon          (dbrk_traceon),
      .itm                   (itm),
      .jdo                   (jdo),
      .jrst_n                (jrst_n),
      .take_action_tracectrl (take_action_tracectrl),
      .trc_ctrl              (trc_ctrl),
      .trc_on                (trc_on),
      .xbrk_traceoff         (xbrk_traceoff),
      .xbrk_traceon          (xbrk_traceon),
      .xbrk_wrap_traceoff    (xbrk_wrap_traceoff)
    );

  snes_tst_cpu_nios2_gen2_0_cpu_nios2_oci_dtrace the_snes_tst_cpu_nios2_gen2_0_cpu_nios2_oci_dtrace
    (
      .atm             (atm),
      .clk             (clk),
      .cpu_d_address   (cpu_d_address),
      .cpu_d_read      (cpu_d_read),
      .cpu_d_readdata  (cpu_d_readdata),
      .cpu_d_wait      (cpu_d_wait),
      .cpu_d_write     (cpu_d_write),
      .cpu_d_writedata (cpu_d_writedata),
      .dtm             (dtm),
      .jrst_n          (jrst_n),
      .trc_ctrl        (trc_ctrl)
    );

  snes_tst_cpu_nios2_gen2_0_cpu_nios2_oci_fifo the_snes_tst_cpu_nios2_gen2_0_cpu_nios2_oci_fifo
    (
      .atm           (atm),
      .clk           (clk),
      .dbrk_traceme  (dbrk_traceme),
      .dbrk_traceoff (dbrk_traceoff),
      .dbrk_traceon  (dbrk_traceon),
      .dtm           (dtm),
      .itm           (itm),
      .jrst_n        (jrst_n),
      .reset_n       (reset_n),
      .trc_on        (trc_on),
      .tw            (tw)
    );

  snes_tst_cpu_nios2_gen2_0_cpu_nios2_oci_pib the_snes_tst_cpu_nios2_gen2_0_cpu_nios2_oci_pib
    (
      .tr_data (tr_data)
    );

  snes_tst_cpu_nios2_gen2_0_cpu_nios2_oci_im the_snes_tst_cpu_nios2_gen2_0_cpu_nios2_oci_im
    (
      .clk                (clk),
      .jrst_n             (jrst_n),
      .tracemem_on        (tracemem_on),
      .tracemem_trcdata   (tracemem_trcdata),
      .tracemem_tw        (tracemem_tw),
      .trc_ctrl           (trc_ctrl),
      .trc_im_addr        (trc_im_addr),
      .trc_wrap           (trc_wrap),
      .tw                 (tw),
      .xbrk_wrap_traceoff (xbrk_wrap_traceoff)
    );

  snes_tst_cpu_nios2_gen2_0_cpu_nios2_avalon_reg the_snes_tst_cpu_nios2_gen2_0_cpu_nios2_avalon_reg
    (
      .address              (address),
      .clk                  (clk),
      .debugaccess          (debugaccess),
      .monitor_error        (monitor_error),
      .monitor_go           (monitor_go),
      .monitor_ready        (monitor_ready),
      .oci_ienable          (oci_ienable),
      .oci_reg_readdata     (oci_reg_readdata),
      .oci_single_step_mode (oci_single_step_mode),
      .ocireg_ers           (ocireg_ers),
      .ocireg_mrs           (ocireg_mrs),
      .reset_n              (reset_n),
      .take_action_ocireg   (take_action_ocireg),
      .write                (write),
      .writedata            (writedata)
    );

  snes_tst_cpu_nios2_gen2_0_cpu_nios2_ocimem the_snes_tst_cpu_nios2_gen2_0_cpu_nios2_ocimem
    (
      .MonDReg                 (MonDReg),
      .address                 (address),
      .byteenable              (byteenable),
      .clk                     (clk),
      .debugaccess             (debugaccess),
      .jdo                     (jdo),
      .jrst_n                  (jrst_n),
      .ociram_readdata         (ociram_readdata),
      .read                    (read),
      .reset_req               (reset_req),
      .take_action_ocimem_a    (take_action_ocimem_a),
      .take_action_ocimem_b    (take_action_ocimem_b),
      .take_no_action_ocimem_a (take_no_action_ocimem_a),
      .waitrequest             (waitrequest),
      .write                   (write),
      .writedata               (writedata)
    );

  assign trigout = dbrk_trigout | xbrk_trigout;
  assign debug_mem_slave_debugaccess_to_roms = debugack;
  always @(posedge clk or negedge jrst_n)
    begin
      if (jrst_n == 0)
          address <= 0;
      else 
        address <= address_nxt;
    end


  always @(posedge clk or negedge jrst_n)
    begin
      if (jrst_n == 0)
          byteenable <= 0;
      else 
        byteenable <= byteenable_nxt;
    end


  always @(posedge clk or negedge jrst_n)
    begin
      if (jrst_n == 0)
          writedata <= 0;
      else 
        writedata <= writedata_nxt;
    end


  always @(posedge clk or negedge jrst_n)
    begin
      if (jrst_n == 0)
          debugaccess <= 0;
      else 
        debugaccess <= debugaccess_nxt;
    end


  always @(posedge clk or negedge jrst_n)
    begin
      if (jrst_n == 0)
          read <= 0;
      else 
        read <= read ? waitrequest : read_nxt;
    end


  always @(posedge clk or negedge jrst_n)
    begin
      if (jrst_n == 0)
          write <= 0;
      else 
        write <= write ? waitrequest : write_nxt;
    end


  always @(posedge clk or negedge jrst_n)
    begin
      if (jrst_n == 0)
          readdata <= 0;
      else 
        readdata <= address[8] ? oci_reg_readdata : ociram_readdata;
    end


  snes_tst_cpu_nios2_gen2_0_cpu_debug_slave_wrapper the_snes_tst_cpu_nios2_gen2_0_cpu_debug_slave_wrapper
    (
      .MonDReg                 (MonDReg),
      .break_readreg           (break_readreg),
      .clk                     (clk),
      .dbrk_hit0_latch         (dbrk_hit0_latch),
      .dbrk_hit1_latch         (dbrk_hit1_latch),
      .dbrk_hit2_latch         (dbrk_hit2_latch),
      .dbrk_hit3_latch         (dbrk_hit3_latch),
      .debugack                (debugack),
      .jdo                     (jdo),
      .jrst_n                  (jrst_n),
      .monitor_error           (monitor_error),
      .monitor_ready           (monitor_ready),
      .reset_n                 (reset_n),
      .resetlatch              (resetlatch),
      .st_ready_test_idle      (st_ready_test_idle),
      .take_action_break_a     (take_action_break_a),
      .take_action_break_b     (take_action_break_b),
      .take_action_break_c     (take_action_break_c),
      .take_action_ocimem_a    (take_action_ocimem_a),
      .take_action_ocimem_b    (take_action_ocimem_b),
      .take_action_tracectrl   (take_action_tracectrl),
      .take_no_action_break_a  (take_no_action_break_a),
      .take_no_action_break_b  (take_no_action_break_b),
      .take_no_action_break_c  (take_no_action_break_c),
      .take_no_action_ocimem_a (take_no_action_ocimem_a),
      .tracemem_on             (tracemem_on),
      .tracemem_trcdata        (tracemem_trcdata),
      .tracemem_tw             (tracemem_tw),
      .trc_im_addr             (trc_im_addr),
      .trc_on                  (trc_on),
      .trc_wrap                (trc_wrap),
      .trigbrktype             (trigbrktype),
      .trigger_state_1         (trigger_state_1)
    );

  //dummy sink, which is an e_mux
  assign dummy_sink = tr_data |
    trigout |
    debugack;

  assign debugreq = 0;

endmodule


// synthesis translate_off
`timescale 1ns / 1ps
// synthesis translate_on

// turn off superfluous verilog processor warnings 
// altera message_level Level1 
// altera message_off 10034 10035 10036 10037 10230 10240 10030 

module snes_tst_cpu_nios2_gen2_0_cpu (
                                       // inputs:
                                        clk,
                                        d_readdata,
                                        d_waitrequest,
                                        debug_mem_slave_address,
                                        debug_mem_slave_byteenable,
                                        debug_mem_slave_debugaccess,
                                        debug_mem_slave_read,
                                        debug_mem_slave_write,
                                        debug_mem_slave_writedata,
                                        i_readdata,
                                        i_waitrequest,
                                        irq,
                                        reset_n,
                                        reset_req,

                                       // outputs:
                                        d_address,
                                        d_byteenable,
                                        d_read,
                                        d_write,
                                        d_writedata,
                                        debug_mem_slave_debugaccess_to_roms,
                                        debug_mem_slave_readdata,
                                        debug_mem_slave_waitrequest,
                                        debug_reset_request,
                                        dummy_ci_port,
                                        i_address,
                                        i_read
                                     )
;

  output  [ 19: 0] d_address;
  output  [  3: 0] d_byteenable;
  output           d_read;
  output           d_write;
  output  [ 31: 0] d_writedata;
  output           debug_mem_slave_debugaccess_to_roms;
  output  [ 31: 0] debug_mem_slave_readdata;
  output           debug_mem_slave_waitrequest;
  output           debug_reset_request;
  output           dummy_ci_port;
  output  [ 19: 0] i_address;
  output           i_read;
  input            clk;
  input   [ 31: 0] d_readdata;
  input            d_waitrequest;
  input   [  8: 0] debug_mem_slave_address;
  input   [  3: 0] debug_mem_slave_byteenable;
  input            debug_mem_slave_debugaccess;
  input            debug_mem_slave_read;
  input            debug_mem_slave_write;
  input   [ 31: 0] debug_mem_slave_writedata;
  input   [ 31: 0] i_readdata;
  input            i_waitrequest;
  input   [ 31: 0] irq;
  input            reset_n;
  input            reset_req;
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
