Opatusos/SNES_TST/Firmware/ip/snes_tst_cpu/synthesis/snes_tst_cpu.v

// snes_tst_cpu.v

// Generated using ACDS version 20.1 720

`timescale 1 ps / 1 ps
module snes_tst_cpu (
		input  wire        clk_clk,              //           clk.clk
		input  wire [31:0] config_input_export,  //  config_input.export
		output wire [31:0] config_output_export, // config_output.export
		input  wire [15:0] cont_data_export,     //     cont_data.export
		output wire [22:0] osd_ram_export,       //       osd_ram.export
		input  wire        reset_reset_n         //         reset.reset_n
	);

	wire  [31:0] nios2_gen2_0_data_master_readdata;                           // mm_interconnect_0:nios2_gen2_0_data_master_readdata -> nios2_gen2_0:d_readdata
	wire         nios2_gen2_0_data_master_waitrequest;                        // mm_interconnect_0:nios2_gen2_0_data_master_waitrequest -> nios2_gen2_0:d_waitrequest
	wire         nios2_gen2_0_data_master_debugaccess;                        // nios2_gen2_0:debug_mem_slave_debugaccess_to_roms -> mm_interconnect_0:nios2_gen2_0_data_master_debugaccess
	wire  [19:0] nios2_gen2_0_data_master_address;                            // nios2_gen2_0:d_address -> mm_interconnect_0:nios2_gen2_0_data_master_address
	wire   [3:0] nios2_gen2_0_data_master_byteenable;                         // nios2_gen2_0:d_byteenable -> mm_interconnect_0:nios2_gen2_0_data_master_byteenable
	wire         nios2_gen2_0_data_master_read;                               // nios2_gen2_0:d_read -> mm_interconnect_0:nios2_gen2_0_data_master_read
	wire         nios2_gen2_0_data_master_write;                              // nios2_gen2_0:d_write -> mm_interconnect_0:nios2_gen2_0_data_master_write
	wire  [31:0] nios2_gen2_0_data_master_writedata;                          // nios2_gen2_0:d_writedata -> mm_interconnect_0:nios2_gen2_0_data_master_writedata
	wire  [31:0] nios2_gen2_0_instruction_master_readdata;                    // mm_interconnect_0:nios2_gen2_0_instruction_master_readdata -> nios2_gen2_0:i_readdata
	wire         nios2_gen2_0_instruction_master_waitrequest;                 // mm_interconnect_0:nios2_gen2_0_instruction_master_waitrequest -> nios2_gen2_0:i_waitrequest
	wire  [19:0] nios2_gen2_0_instruction_master_address;                     // nios2_gen2_0:i_address -> mm_interconnect_0:nios2_gen2_0_instruction_master_address
	wire         nios2_gen2_0_instruction_master_read;                        // nios2_gen2_0:i_read -> mm_interconnect_0:nios2_gen2_0_instruction_master_read
	wire         mm_interconnect_0_jtag_uart_0_avalon_jtag_slave_chipselect;  // mm_interconnect_0:jtag_uart_0_avalon_jtag_slave_chipselect -> jtag_uart_0:av_chipselect
	wire  [31:0] mm_interconnect_0_jtag_uart_0_avalon_jtag_slave_readdata;    // jtag_uart_0:av_readdata -> mm_interconnect_0:jtag_uart_0_avalon_jtag_slave_readdata
	wire         mm_interconnect_0_jtag_uart_0_avalon_jtag_slave_waitrequest; // jtag_uart_0:av_waitrequest -> mm_interconnect_0:jtag_uart_0_avalon_jtag_slave_waitrequest
	wire   [0:0] mm_interconnect_0_jtag_uart_0_avalon_jtag_slave_address;     // mm_interconnect_0:jtag_uart_0_avalon_jtag_slave_address -> jtag_uart_0:av_address
	wire         mm_interconnect_0_jtag_uart_0_avalon_jtag_slave_read;        // mm_interconnect_0:jtag_uart_0_avalon_jtag_slave_read -> jtag_uart_0:av_read_n
	wire         mm_interconnect_0_jtag_uart_0_avalon_jtag_slave_write;       // mm_interconnect_0:jtag_uart_0_avalon_jtag_slave_write -> jtag_uart_0:av_write_n
	wire  [31:0] mm_interconnect_0_jtag_uart_0_avalon_jtag_slave_writedata;   // mm_interconnect_0:jtag_uart_0_avalon_jtag_slave_writedata -> jtag_uart_0:av_writedata
	wire  [31:0] mm_interconnect_0_onchip_flash_0_csr_readdata;               // onchip_flash_0:avmm_csr_readdata -> mm_interconnect_0:onchip_flash_0_csr_readdata
	wire   [0:0] mm_interconnect_0_onchip_flash_0_csr_address;                // mm_interconnect_0:onchip_flash_0_csr_address -> onchip_flash_0:avmm_csr_addr
	wire         mm_interconnect_0_onchip_flash_0_csr_read;                   // mm_interconnect_0:onchip_flash_0_csr_read -> onchip_flash_0:avmm_csr_read
	wire         mm_interconnect_0_onchip_flash_0_csr_write;                  // mm_interconnect_0:onchip_flash_0_csr_write -> onchip_flash_0:avmm_csr_write
	wire  [31:0] mm_interconnect_0_onchip_flash_0_csr_writedata;              // mm_interconnect_0:onchip_flash_0_csr_writedata -> onchip_flash_0:avmm_csr_writedata
	wire  [31:0] mm_interconnect_0_onchip_flash_0_data_readdata;              // onchip_flash_0:avmm_data_readdata -> mm_interconnect_0:onchip_flash_0_data_readdata
	wire         mm_interconnect_0_onchip_flash_0_data_waitrequest;           // onchip_flash_0:avmm_data_waitrequest -> mm_interconnect_0:onchip_flash_0_data_waitrequest
	wire  [16:0] mm_interconnect_0_onchip_flash_0_data_address;               // mm_interconnect_0:onchip_flash_0_data_address -> onchip_flash_0:avmm_data_addr
	wire         mm_interconnect_0_onchip_flash_0_data_read;                  // mm_interconnect_0:onchip_flash_0_data_read -> onchip_flash_0:avmm_data_read
	wire         mm_interconnect_0_onchip_flash_0_data_readdatavalid;         // onchip_flash_0:avmm_data_readdatavalid -> mm_interconnect_0:onchip_flash_0_data_readdatavalid
	wire         mm_interconnect_0_onchip_flash_0_data_write;                 // mm_interconnect_0:onchip_flash_0_data_write -> onchip_flash_0:avmm_data_write
	wire  [31:0] mm_interconnect_0_onchip_flash_0_data_writedata;             // mm_interconnect_0:onchip_flash_0_data_writedata -> onchip_flash_0:avmm_data_writedata
	wire   [3:0] mm_interconnect_0_onchip_flash_0_data_burstcount;            // mm_interconnect_0:onchip_flash_0_data_burstcount -> onchip_flash_0:avmm_data_burstcount
	wire  [31:0] mm_interconnect_0_nios2_gen2_0_debug_mem_slave_readdata;     // nios2_gen2_0:debug_mem_slave_readdata -> mm_interconnect_0:nios2_gen2_0_debug_mem_slave_readdata
	wire         mm_interconnect_0_nios2_gen2_0_debug_mem_slave_waitrequest;  // nios2_gen2_0:debug_mem_slave_waitrequest -> mm_interconnect_0:nios2_gen2_0_debug_mem_slave_waitrequest
	wire         mm_interconnect_0_nios2_gen2_0_debug_mem_slave_debugaccess;  // mm_interconnect_0:nios2_gen2_0_debug_mem_slave_debugaccess -> nios2_gen2_0:debug_mem_slave_debugaccess
	wire   [8:0] mm_interconnect_0_nios2_gen2_0_debug_mem_slave_address;      // mm_interconnect_0:nios2_gen2_0_debug_mem_slave_address -> nios2_gen2_0:debug_mem_slave_address
	wire         mm_interconnect_0_nios2_gen2_0_debug_mem_slave_read;         // mm_interconnect_0:nios2_gen2_0_debug_mem_slave_read -> nios2_gen2_0:debug_mem_slave_read
	wire   [3:0] mm_interconnect_0_nios2_gen2_0_debug_mem_slave_byteenable;   // mm_interconnect_0:nios2_gen2_0_debug_mem_slave_byteenable -> nios2_gen2_0:debug_mem_slave_byteenable
	wire         mm_interconnect_0_nios2_gen2_0_debug_mem_slave_write;        // mm_interconnect_0:nios2_gen2_0_debug_mem_slave_write -> nios2_gen2_0:debug_mem_slave_write
	wire  [31:0] mm_interconnect_0_nios2_gen2_0_debug_mem_slave_writedata;    // mm_interconnect_0:nios2_gen2_0_debug_mem_slave_writedata -> nios2_gen2_0:debug_mem_slave_writedata
	wire         mm_interconnect_0_onchip_memory2_0_s1_chipselect;            // mm_interconnect_0:onchip_memory2_0_s1_chipselect -> onchip_memory2_0:chipselect
	wire  [31:0] mm_interconnect_0_onchip_memory2_0_s1_readdata;              // onchip_memory2_0:readdata -> mm_interconnect_0:onchip_memory2_0_s1_readdata
	wire  [10:0] mm_interconnect_0_onchip_memory2_0_s1_address;               // mm_interconnect_0:onchip_memory2_0_s1_address -> onchip_memory2_0:address
	wire   [3:0] mm_interconnect_0_onchip_memory2_0_s1_byteenable;            // mm_interconnect_0:onchip_memory2_0_s1_byteenable -> onchip_memory2_0:byteenable
	wire         mm_interconnect_0_onchip_memory2_0_s1_write;                 // mm_interconnect_0:onchip_memory2_0_s1_write -> onchip_memory2_0:write
	wire  [31:0] mm_interconnect_0_onchip_memory2_0_s1_writedata;             // mm_interconnect_0:onchip_memory2_0_s1_writedata -> onchip_memory2_0:writedata
	wire         mm_interconnect_0_onchip_memory2_0_s1_clken;                 // mm_interconnect_0:onchip_memory2_0_s1_clken -> onchip_memory2_0:clken
	wire  [31:0] mm_interconnect_0_config_input_s1_readdata;                  // config_input:readdata -> mm_interconnect_0:config_input_s1_readdata
	wire   [1:0] mm_interconnect_0_config_input_s1_address;                   // mm_interconnect_0:config_input_s1_address -> config_input:address
	wire         mm_interconnect_0_config_output_s1_chipselect;               // mm_interconnect_0:config_output_s1_chipselect -> config_output:chipselect
	wire  [31:0] mm_interconnect_0_config_output_s1_readdata;                 // config_output:readdata -> mm_interconnect_0:config_output_s1_readdata
	wire   [2:0] mm_interconnect_0_config_output_s1_address;                  // mm_interconnect_0:config_output_s1_address -> config_output:address
	wire         mm_interconnect_0_config_output_s1_write;                    // mm_interconnect_0:config_output_s1_write -> config_output:write_n
	wire  [31:0] mm_interconnect_0_config_output_s1_writedata;                // mm_interconnect_0:config_output_s1_writedata -> config_output:writedata
	wire         mm_interconnect_0_osd_ram_s1_chipselect;                     // mm_interconnect_0:osd_ram_s1_chipselect -> osd_ram:chipselect
	wire  [31:0] mm_interconnect_0_osd_ram_s1_readdata;                       // osd_ram:readdata -> mm_interconnect_0:osd_ram_s1_readdata
	wire   [2:0] mm_interconnect_0_osd_ram_s1_address;                        // mm_interconnect_0:osd_ram_s1_address -> osd_ram:address
	wire         mm_interconnect_0_osd_ram_s1_write;                          // mm_interconnect_0:osd_ram_s1_write -> osd_ram:write_n
	wire  [31:0] mm_interconnect_0_osd_ram_s1_writedata;                      // mm_interconnect_0:osd_ram_s1_writedata -> osd_ram:writedata
	wire  [31:0] mm_interconnect_0_controller_data_s1_readdata;               // controller_data:readdata -> mm_interconnect_0:controller_data_s1_readdata
	wire   [1:0] mm_interconnect_0_controller_data_s1_address;                // mm_interconnect_0:controller_data_s1_address -> controller_data:address
	wire         irq_mapper_receiver0_irq;                                    // jtag_uart_0:av_irq -> irq_mapper:receiver0_irq
	wire  [31:0] nios2_gen2_0_irq_irq;                                        // irq_mapper:sender_irq -> nios2_gen2_0:irq
	wire         rst_controller_reset_out_reset;                              // rst_controller:reset_out -> [config_input:reset_n, config_output:reset_n, controller_data:reset_n, irq_mapper:reset, jtag_uart_0:rst_n, mm_interconnect_0:nios2_gen2_0_reset_reset_bridge_in_reset_reset, nios2_gen2_0:reset_n, onchip_flash_0:reset_n, onchip_memory2_0:reset, osd_ram:reset_n, rst_translator:in_reset]
	wire         rst_controller_reset_out_reset_req;                          // rst_controller:reset_req -> [nios2_gen2_0:reset_req, onchip_memory2_0:reset_req, rst_translator:reset_req_in]
	wire         nios2_gen2_0_debug_reset_request_reset;                      // nios2_gen2_0:debug_reset_request -> rst_controller:reset_in1

	snes_tst_cpu_config_input config_input (
		.clk      (clk_clk),                                    //                 clk.clk
		.reset_n  (~rst_controller_reset_out_reset),            //               reset.reset_n
		.address  (mm_interconnect_0_config_input_s1_address),  //                  s1.address
		.readdata (mm_interconnect_0_config_input_s1_readdata), //                    .readdata
		.in_port  (config_input_export)                         // external_connection.export
	);

	snes_tst_cpu_config_output config_output (
		.clk        (clk_clk),                                       //                 clk.clk
		.reset_n    (~rst_controller_reset_out_reset),               //               reset.reset_n
		.address    (mm_interconnect_0_config_output_s1_address),    //                  s1.address
		.write_n    (~mm_interconnect_0_config_output_s1_write),     //                    .write_n
		.writedata  (mm_interconnect_0_config_output_s1_writedata),  //                    .writedata
		.chipselect (mm_interconnect_0_config_output_s1_chipselect), //                    .chipselect
		.readdata   (mm_interconnect_0_config_output_s1_readdata),   //                    .readdata
		.out_port   (config_output_export)                           // external_connection.export
	);

	snes_tst_cpu_controller_data controller_data (
		.clk      (clk_clk),                                       //                 clk.clk
		.reset_n  (~rst_controller_reset_out_reset),               //               reset.reset_n
		.address  (mm_interconnect_0_controller_data_s1_address),  //                  s1.address
		.readdata (mm_interconnect_0_controller_data_s1_readdata), //                    .readdata
		.in_port  (cont_data_export)                               // external_connection.export
	);

	snes_tst_cpu_jtag_uart_0 jtag_uart_0 (
		.clk            (clk_clk),                                                     //               clk.clk
		.rst_n          (~rst_controller_reset_out_reset),                             //             reset.reset_n
		.av_chipselect  (mm_interconnect_0_jtag_uart_0_avalon_jtag_slave_chipselect),  // avalon_jtag_slave.chipselect
		.av_address     (mm_interconnect_0_jtag_uart_0_avalon_jtag_slave_address),     //                  .address
		.av_read_n      (~mm_interconnect_0_jtag_uart_0_avalon_jtag_slave_read),       //                  .read_n
		.av_readdata    (mm_interconnect_0_jtag_uart_0_avalon_jtag_slave_readdata),    //                  .readdata
		.av_write_n     (~mm_interconnect_0_jtag_uart_0_avalon_jtag_slave_write),      //                  .write_n
		.av_writedata   (mm_interconnect_0_jtag_uart_0_avalon_jtag_slave_writedata),   //                  .writedata
		.av_waitrequest (mm_interconnect_0_jtag_uart_0_avalon_jtag_slave_waitrequest), //                  .waitrequest
		.av_irq         (irq_mapper_receiver0_irq)                                     //               irq.irq
	);

	snes_tst_cpu_nios2_gen2_0 nios2_gen2_0 (
		.clk                                 (clk_clk),                                                    //                       clk.clk
		.reset_n                             (~rst_controller_reset_out_reset),                            //                     reset.reset_n
		.reset_req                           (rst_controller_reset_out_reset_req),                         //                          .reset_req
		.d_address                           (nios2_gen2_0_data_master_address),                           //               data_master.address
		.d_byteenable                        (nios2_gen2_0_data_master_byteenable),                        //                          .byteenable
		.d_read                              (nios2_gen2_0_data_master_read),                              //                          .read
		.d_readdata                          (nios2_gen2_0_data_master_readdata),                          //                          .readdata
		.d_waitrequest                       (nios2_gen2_0_data_master_waitrequest),                       //                          .waitrequest
		.d_write                             (nios2_gen2_0_data_master_write),                             //                          .write
		.d_writedata                         (nios2_gen2_0_data_master_writedata),                         //                          .writedata
		.debug_mem_slave_debugaccess_to_roms (nios2_gen2_0_data_master_debugaccess),                       //                          .debugaccess
		.i_address                           (nios2_gen2_0_instruction_master_address),                    //        instruction_master.address
		.i_read                              (nios2_gen2_0_instruction_master_read),                       //                          .read
		.i_readdata                          (nios2_gen2_0_instruction_master_readdata),                   //                          .readdata
		.i_waitrequest                       (nios2_gen2_0_instruction_master_waitrequest),                //                          .waitrequest
		.irq                                 (nios2_gen2_0_irq_irq),                                       //                       irq.irq
		.debug_reset_request                 (nios2_gen2_0_debug_reset_request_reset),                     //       debug_reset_request.reset
		.debug_mem_slave_address             (mm_interconnect_0_nios2_gen2_0_debug_mem_slave_address),     //           debug_mem_slave.address
		.debug_mem_slave_byteenable          (mm_interconnect_0_nios2_gen2_0_debug_mem_slave_byteenable),  //                          .byteenable
		.debug_mem_slave_debugaccess         (mm_interconnect_0_nios2_gen2_0_debug_mem_slave_debugaccess), //                          .debugaccess
		.debug_mem_slave_read                (mm_interconnect_0_nios2_gen2_0_debug_mem_slave_read),        //                          .read
		.debug_mem_slave_readdata            (mm_interconnect_0_nios2_gen2_0_debug_mem_slave_readdata),    //                          .readdata
		.debug_mem_slave_waitrequest         (mm_interconnect_0_nios2_gen2_0_debug_mem_slave_waitrequest), //                          .waitrequest
		.debug_mem_slave_write               (mm_interconnect_0_nios2_gen2_0_debug_mem_slave_write),       //                          .write
		.debug_mem_slave_writedata           (mm_interconnect_0_nios2_gen2_0_debug_mem_slave_writedata),   //                          .writedata
		.dummy_ci_port                       ()                                                            // custom_instruction_master.readra
	);

	altera_onchip_flash #(
		.INIT_FILENAME                       (""),
		.INIT_FILENAME_SIM                   (""),
		.DEVICE_FAMILY                       ("MAX 10"),
		.PART_NAME                           ("10M04SAE144C8G"),
		.DEVICE_ID                           ("04"),
		.SECTOR1_START_ADDR                  (0),
		.SECTOR1_END_ADDR                    (4095),
		.SECTOR2_START_ADDR                  (4096),
		.SECTOR2_END_ADDR                    (25087),
		.SECTOR3_START_ADDR                  (25088),
		.SECTOR3_END_ADDR                    (39935),
		.SECTOR4_START_ADDR                  (39936),
		.SECTOR4_END_ADDR                    (75775),
		.SECTOR5_START_ADDR                  (0),
		.SECTOR5_END_ADDR                    (0),
		.MIN_VALID_ADDR                      (0),
		.MAX_VALID_ADDR                      (75775),
		.MIN_UFM_VALID_ADDR                  (0),
		.MAX_UFM_VALID_ADDR                  (4095),
		.SECTOR1_MAP                         (2),
		.SECTOR2_MAP                         (3),
		.SECTOR3_MAP                         (4),
		.SECTOR4_MAP                         (5),
		.SECTOR5_MAP                         (0),
		.ADDR_RANGE1_END_ADDR                (75775),
		.ADDR_RANGE2_END_ADDR                (75775),
		.ADDR_RANGE1_OFFSET                  (4608),
		.ADDR_RANGE2_OFFSET                  (0),
		.ADDR_RANGE3_OFFSET                  (0),
		.AVMM_DATA_ADDR_WIDTH                (17),
		.AVMM_DATA_DATA_WIDTH                (32),
		.AVMM_DATA_BURSTCOUNT_WIDTH          (4),
		.SECTOR_READ_PROTECTION_MODE         (16),
		.FLASH_SEQ_READ_DATA_COUNT           (2),
		.FLASH_ADDR_ALIGNMENT_BITS           (1),
		.FLASH_READ_CYCLE_MAX_INDEX          (4),
		.FLASH_RESET_CYCLE_MAX_INDEX         (5),
		.FLASH_BUSY_TIMEOUT_CYCLE_MAX_INDEX  (25),
		.FLASH_ERASE_TIMEOUT_CYCLE_MAX_INDEX (7517020),
		.FLASH_WRITE_TIMEOUT_CYCLE_MAX_INDEX (6550),
		.PARALLEL_MODE                       (1),
		.READ_AND_WRITE_MODE                 (1),
		.WRAPPING_BURST_MODE                 (0),
		.IS_DUAL_BOOT                        ("False"),
		.IS_ERAM_SKIP                        ("False"),
		.IS_COMPRESSED_IMAGE                 ("False")
	) onchip_flash_0 (
		.clock                   (clk_clk),                                             //    clk.clk
		.reset_n                 (~rst_controller_reset_out_reset),                     // nreset.reset_n
		.avmm_data_addr          (mm_interconnect_0_onchip_flash_0_data_address),       //   data.address
		.avmm_data_read          (mm_interconnect_0_onchip_flash_0_data_read),          //       .read
		.avmm_data_writedata     (mm_interconnect_0_onchip_flash_0_data_writedata),     //       .writedata
		.avmm_data_write         (mm_interconnect_0_onchip_flash_0_data_write),         //       .write
		.avmm_data_readdata      (mm_interconnect_0_onchip_flash_0_data_readdata),      //       .readdata
		.avmm_data_waitrequest   (mm_interconnect_0_onchip_flash_0_data_waitrequest),   //       .waitrequest
		.avmm_data_readdatavalid (mm_interconnect_0_onchip_flash_0_data_readdatavalid), //       .readdatavalid
		.avmm_data_burstcount    (mm_interconnect_0_onchip_flash_0_data_burstcount),    //       .burstcount
		.avmm_csr_addr           (mm_interconnect_0_onchip_flash_0_csr_address),        //    csr.address
		.avmm_csr_read           (mm_interconnect_0_onchip_flash_0_csr_read),           //       .read
		.avmm_csr_writedata      (mm_interconnect_0_onchip_flash_0_csr_writedata),      //       .writedata
		.avmm_csr_write          (mm_interconnect_0_onchip_flash_0_csr_write),          //       .write
		.avmm_csr_readdata       (mm_interconnect_0_onchip_flash_0_csr_readdata)        //       .readdata
	);

	snes_tst_cpu_onchip_memory2_0 onchip_memory2_0 (
		.clk        (clk_clk),                                          //   clk1.clk
		.address    (mm_interconnect_0_onchip_memory2_0_s1_address),    //     s1.address
		.clken      (mm_interconnect_0_onchip_memory2_0_s1_clken),      //       .clken
		.chipselect (mm_interconnect_0_onchip_memory2_0_s1_chipselect), //       .chipselect
		.write      (mm_interconnect_0_onchip_memory2_0_s1_write),      //       .write
		.readdata   (mm_interconnect_0_onchip_memory2_0_s1_readdata),   //       .readdata
		.writedata  (mm_interconnect_0_onchip_memory2_0_s1_writedata),  //       .writedata
		.byteenable (mm_interconnect_0_onchip_memory2_0_s1_byteenable), //       .byteenable
		.reset      (rst_controller_reset_out_reset),                   // reset1.reset
		.reset_req  (rst_controller_reset_out_reset_req),               //       .reset_req
		.freeze     (1'b0)                                              // (terminated)
	);

	snes_tst_cpu_osd_ram osd_ram (
		.clk        (clk_clk),                                 //                 clk.clk
		.reset_n    (~rst_controller_reset_out_reset),         //               reset.reset_n
		.address    (mm_interconnect_0_osd_ram_s1_address),    //                  s1.address
		.write_n    (~mm_interconnect_0_osd_ram_s1_write),     //                    .write_n
		.writedata  (mm_interconnect_0_osd_ram_s1_writedata),  //                    .writedata
		.chipselect (mm_interconnect_0_osd_ram_s1_chipselect), //                    .chipselect
		.readdata   (mm_interconnect_0_osd_ram_s1_readdata),   //                    .readdata
		.out_port   (osd_ram_export)                           // external_connection.export
	);

	snes_tst_cpu_mm_interconnect_0 mm_interconnect_0 (
		.clk_0_clk_clk                                  (clk_clk),                                                     //                                clk_0_clk.clk
		.nios2_gen2_0_reset_reset_bridge_in_reset_reset (rst_controller_reset_out_reset),                              // nios2_gen2_0_reset_reset_bridge_in_reset.reset
		.nios2_gen2_0_data_master_address               (nios2_gen2_0_data_master_address),                            //                 nios2_gen2_0_data_master.address
		.nios2_gen2_0_data_master_waitrequest           (nios2_gen2_0_data_master_waitrequest),                        //                                         .waitrequest
		.nios2_gen2_0_data_master_byteenable            (nios2_gen2_0_data_master_byteenable),                         //                                         .byteenable
		.nios2_gen2_0_data_master_read                  (nios2_gen2_0_data_master_read),                               //                                         .read
		.nios2_gen2_0_data_master_readdata              (nios2_gen2_0_data_master_readdata),                           //                                         .readdata
		.nios2_gen2_0_data_master_write                 (nios2_gen2_0_data_master_write),                              //                                         .write
		.nios2_gen2_0_data_master_writedata             (nios2_gen2_0_data_master_writedata),                          //                                         .writedata
		.nios2_gen2_0_data_master_debugaccess           (nios2_gen2_0_data_master_debugaccess),                        //                                         .debugaccess
		.nios2_gen2_0_instruction_master_address        (nios2_gen2_0_instruction_master_address),                     //          nios2_gen2_0_instruction_master.address
		.nios2_gen2_0_instruction_master_waitrequest    (nios2_gen2_0_instruction_master_waitrequest),                 //                                         .waitrequest
		.nios2_gen2_0_instruction_master_read           (nios2_gen2_0_instruction_master_read),                        //                                         .read
		.nios2_gen2_0_instruction_master_readdata       (nios2_gen2_0_instruction_master_readdata),                    //                                         .readdata
		.config_input_s1_address                        (mm_interconnect_0_config_input_s1_address),                   //                          config_input_s1.address
		.config_input_s1_readdata                       (mm_interconnect_0_config_input_s1_readdata),                  //                                         .readdata
		.config_output_s1_address                       (mm_interconnect_0_config_output_s1_address),                  //                         config_output_s1.address
		.config_output_s1_write                         (mm_interconnect_0_config_output_s1_write),                    //                                         .write
		.config_output_s1_readdata                      (mm_interconnect_0_config_output_s1_readdata),                 //                                         .readdata
		.config_output_s1_writedata                     (mm_interconnect_0_config_output_s1_writedata),                //                                         .writedata
		.config_output_s1_chipselect                    (mm_interconnect_0_config_output_s1_chipselect),               //                                         .chipselect
		.controller_data_s1_address                     (mm_interconnect_0_controller_data_s1_address),                //                       controller_data_s1.address
		.controller_data_s1_readdata                    (mm_interconnect_0_controller_data_s1_readdata),               //                                         .readdata
		.jtag_uart_0_avalon_jtag_slave_address          (mm_interconnect_0_jtag_uart_0_avalon_jtag_slave_address),     //            jtag_uart_0_avalon_jtag_slave.address
		.jtag_uart_0_avalon_jtag_slave_write            (mm_interconnect_0_jtag_uart_0_avalon_jtag_slave_write),       //                                         .write
		.jtag_uart_0_avalon_jtag_slave_read             (mm_interconnect_0_jtag_uart_0_avalon_jtag_slave_read),        //                                         .read
		.jtag_uart_0_avalon_jtag_slave_readdata         (mm_interconnect_0_jtag_uart_0_avalon_jtag_slave_readdata),    //                                         .readdata
		.jtag_uart_0_avalon_jtag_slave_writedata        (mm_interconnect_0_jtag_uart_0_avalon_jtag_slave_writedata),   //                                         .writedata
		.jtag_uart_0_avalon_jtag_slave_waitrequest      (mm_interconnect_0_jtag_uart_0_avalon_jtag_slave_waitrequest), //                                         .waitrequest
		.jtag_uart_0_avalon_jtag_slave_chipselect       (mm_interconnect_0_jtag_uart_0_avalon_jtag_slave_chipselect),  //                                         .chipselect
		.nios2_gen2_0_debug_mem_slave_address           (mm_interconnect_0_nios2_gen2_0_debug_mem_slave_address),      //             nios2_gen2_0_debug_mem_slave.address
		.nios2_gen2_0_debug_mem_slave_write             (mm_interconnect_0_nios2_gen2_0_debug_mem_slave_write),        //                                         .write
		.nios2_gen2_0_debug_mem_slave_read              (mm_interconnect_0_nios2_gen2_0_debug_mem_slave_read),         //                                         .read
		.nios2_gen2_0_debug_mem_slave_readdata          (mm_interconnect_0_nios2_gen2_0_debug_mem_slave_readdata),     //                                         .readdata
		.nios2_gen2_0_debug_mem_slave_writedata         (mm_interconnect_0_nios2_gen2_0_debug_mem_slave_writedata),    //                                         .writedata
		.nios2_gen2_0_debug_mem_slave_byteenable        (mm_interconnect_0_nios2_gen2_0_debug_mem_slave_byteenable),   //                                         .byteenable
		.nios2_gen2_0_debug_mem_slave_waitrequest       (mm_interconnect_0_nios2_gen2_0_debug_mem_slave_waitrequest),  //                                         .waitrequest
		.nios2_gen2_0_debug_mem_slave_debugaccess       (mm_interconnect_0_nios2_gen2_0_debug_mem_slave_debugaccess),  //                                         .debugaccess
		.onchip_flash_0_csr_address                     (mm_interconnect_0_onchip_flash_0_csr_address),                //                       onchip_flash_0_csr.address
		.onchip_flash_0_csr_write                       (mm_interconnect_0_onchip_flash_0_csr_write),                  //                                         .write
		.onchip_flash_0_csr_read                        (mm_interconnect_0_onchip_flash_0_csr_read),                   //                                         .read
		.onchip_flash_0_csr_readdata                    (mm_interconnect_0_onchip_flash_0_csr_readdata),               //                                         .readdata
		.onchip_flash_0_csr_writedata                   (mm_interconnect_0_onchip_flash_0_csr_writedata),              //                                         .writedata
		.onchip_flash_0_data_address                    (mm_interconnect_0_onchip_flash_0_data_address),               //                      onchip_flash_0_data.address
		.onchip_flash_0_data_write                      (mm_interconnect_0_onchip_flash_0_data_write),                 //                                         .write
		.onchip_flash_0_data_read                       (mm_interconnect_0_onchip_flash_0_data_read),                  //                                         .read
		.onchip_flash_0_data_readdata                   (mm_interconnect_0_onchip_flash_0_data_readdata),              //                                         .readdata
		.onchip_flash_0_data_writedata                  (mm_interconnect_0_onchip_flash_0_data_writedata),             //                                         .writedata
		.onchip_flash_0_data_burstcount                 (mm_interconnect_0_onchip_flash_0_data_burstcount),            //                                         .burstcount
		.onchip_flash_0_data_readdatavalid              (mm_interconnect_0_onchip_flash_0_data_readdatavalid),         //                                         .readdatavalid
		.onchip_flash_0_data_waitrequest                (mm_interconnect_0_onchip_flash_0_data_waitrequest),           //                                         .waitrequest
		.onchip_memory2_0_s1_address                    (mm_interconnect_0_onchip_memory2_0_s1_address),               //                      onchip_memory2_0_s1.address
		.onchip_memory2_0_s1_write                      (mm_interconnect_0_onchip_memory2_0_s1_write),                 //                                         .write
		.onchip_memory2_0_s1_readdata                   (mm_interconnect_0_onchip_memory2_0_s1_readdata),              //                                         .readdata
		.onchip_memory2_0_s1_writedata                  (mm_interconnect_0_onchip_memory2_0_s1_writedata),             //                                         .writedata
		.onchip_memory2_0_s1_byteenable                 (mm_interconnect_0_onchip_memory2_0_s1_byteenable),            //                                         .byteenable
		.onchip_memory2_0_s1_chipselect                 (mm_interconnect_0_onchip_memory2_0_s1_chipselect),            //                                         .chipselect
		.onchip_memory2_0_s1_clken                      (mm_interconnect_0_onchip_memory2_0_s1_clken),                 //                                         .clken
		.osd_ram_s1_address                             (mm_interconnect_0_osd_ram_s1_address),                        //                               osd_ram_s1.address
		.osd_ram_s1_write                               (mm_interconnect_0_osd_ram_s1_write),                          //                                         .write
		.osd_ram_s1_readdata                            (mm_interconnect_0_osd_ram_s1_readdata),                       //                                         .readdata
		.osd_ram_s1_writedata                           (mm_interconnect_0_osd_ram_s1_writedata),                      //                                         .writedata
		.osd_ram_s1_chipselect                          (mm_interconnect_0_osd_ram_s1_chipselect)                      //                                         .chipselect
	);

	snes_tst_cpu_irq_mapper irq_mapper (
		.clk           (clk_clk),                        //       clk.clk
		.reset         (rst_controller_reset_out_reset), // clk_reset.reset
		.receiver0_irq (irq_mapper_receiver0_irq),       // receiver0.irq
		.sender_irq    (nios2_gen2_0_irq_irq)            //    sender.irq
	);

	altera_reset_controller #(
		.NUM_RESET_INPUTS          (2),
		.OUTPUT_RESET_SYNC_EDGES   ("deassert"),
		.SYNC_DEPTH                (2),
		.RESET_REQUEST_PRESENT     (1),
		.RESET_REQ_WAIT_TIME       (1),
		.MIN_RST_ASSERTION_TIME    (3),
		.RESET_REQ_EARLY_DSRT_TIME (1),
		.USE_RESET_REQUEST_IN0     (0),
		.USE_RESET_REQUEST_IN1     (0),
		.USE_RESET_REQUEST_IN2     (0),
		.USE_RESET_REQUEST_IN3     (0),
		.USE_RESET_REQUEST_IN4     (0),
		.USE_RESET_REQUEST_IN5     (0),
		.USE_RESET_REQUEST_IN6     (0),
		.USE_RESET_REQUEST_IN7     (0),
		.USE_RESET_REQUEST_IN8     (0),
		.USE_RESET_REQUEST_IN9     (0),
		.USE_RESET_REQUEST_IN10    (0),
		.USE_RESET_REQUEST_IN11    (0),
		.USE_RESET_REQUEST_IN12    (0),
		.USE_RESET_REQUEST_IN13    (0),
		.USE_RESET_REQUEST_IN14    (0),
		.USE_RESET_REQUEST_IN15    (0),
		.ADAPT_RESET_REQUEST       (0)
	) rst_controller (
		.reset_in0      (~reset_reset_n),                         // reset_in0.reset
		.reset_in1      (nios2_gen2_0_debug_reset_request_reset), // reset_in1.reset
		.clk            (clk_clk),                                //       clk.clk
		.reset_out      (rst_controller_reset_out_reset),         // reset_out.reset
		.reset_req      (rst_controller_reset_out_reset_req),     //          .reset_req
		.reset_req_in0  (1'b0),                                   // (terminated)
		.reset_req_in1  (1'b0),                                   // (terminated)
		.reset_in2      (1'b0),                                   // (terminated)
		.reset_req_in2  (1'b0),                                   // (terminated)
		.reset_in3      (1'b0),                                   // (terminated)
		.reset_req_in3  (1'b0),                                   // (terminated)
		.reset_in4      (1'b0),                                   // (terminated)
		.reset_req_in4  (1'b0),                                   // (terminated)
		.reset_in5      (1'b0),                                   // (terminated)
		.reset_req_in5  (1'b0),                                   // (terminated)
		.reset_in6      (1'b0),                                   // (terminated)
		.reset_req_in6  (1'b0),                                   // (terminated)
		.reset_in7      (1'b0),                                   // (terminated)
		.reset_req_in7  (1'b0),                                   // (terminated)
		.reset_in8      (1'b0),                                   // (terminated)
		.reset_req_in8  (1'b0),                                   // (terminated)
		.reset_in9      (1'b0),                                   // (terminated)
		.reset_req_in9  (1'b0),                                   // (terminated)
		.reset_in10     (1'b0),                                   // (terminated)
		.reset_req_in10 (1'b0),                                   // (terminated)
		.reset_in11     (1'b0),                                   // (terminated)
		.reset_req_in11 (1'b0),                                   // (terminated)
		.reset_in12     (1'b0),                                   // (terminated)
		.reset_req_in12 (1'b0),                                   // (terminated)
		.reset_in13     (1'b0),                                   // (terminated)
		.reset_req_in13 (1'b0),                                   // (terminated)
		.reset_in14     (1'b0),                                   // (terminated)
		.reset_req_in14 (1'b0),                                   // (terminated)
		.reset_in15     (1'b0),                                   // (terminated)
		.reset_req_in15 (1'b0)                                    // (terminated)
	);

endmodule
